wdathing/coco3-case-project/stl/main_top_right.stl

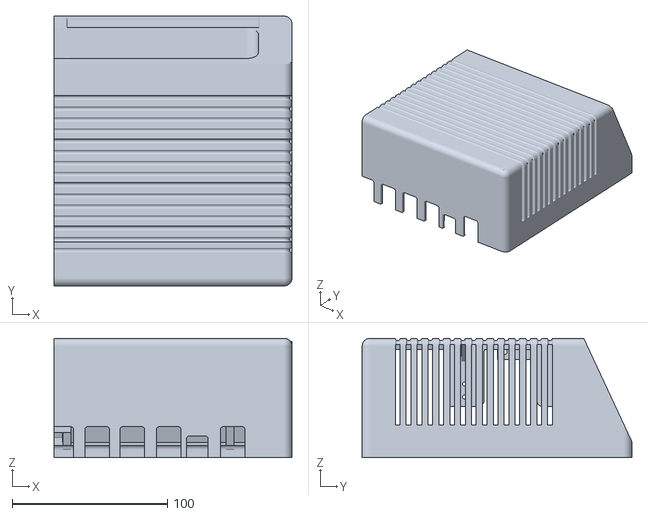
[picture p21: CAD file, 2026-10-01]
stl/main_top_right.stl
153.2 x 173.6 x 76.8
