wdathing/coco3-case-project/stl/bezel_artemis_whole.stl

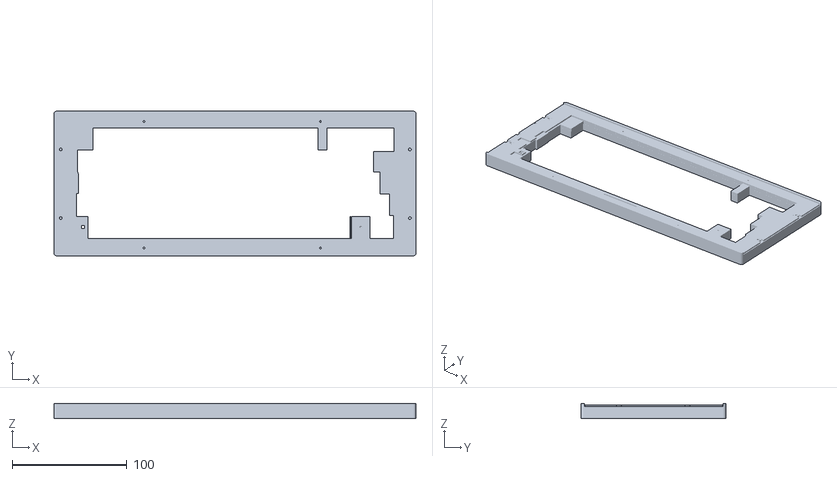
[picture p22: CAD file, 2026-09-28]
stl/bezel_artemis_whole.stl
316.0 x 126.2 x 13.3
