wdathing/coco3-case-project/stl/bezel_oem_whole.stl

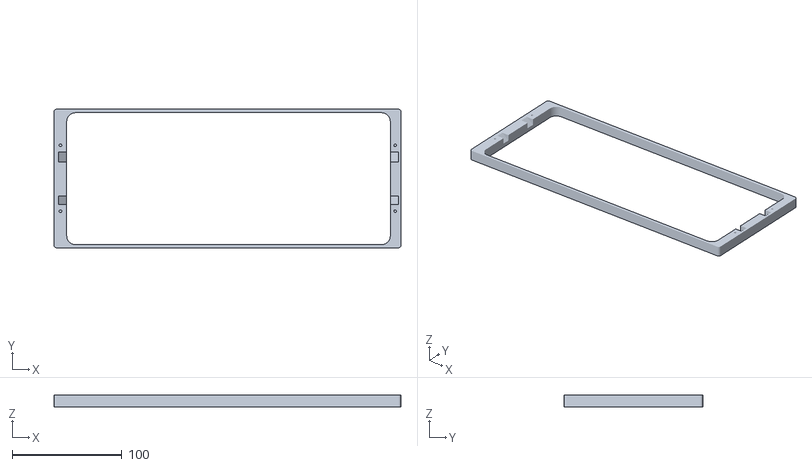
[picture p23: CAD file, 2026-09-28]
stl/bezel_oem_whole.stl
316.0 x 126.2 x 10.6
