wdathing/coco3-case-project/stl/keyboard_main_keys.stl

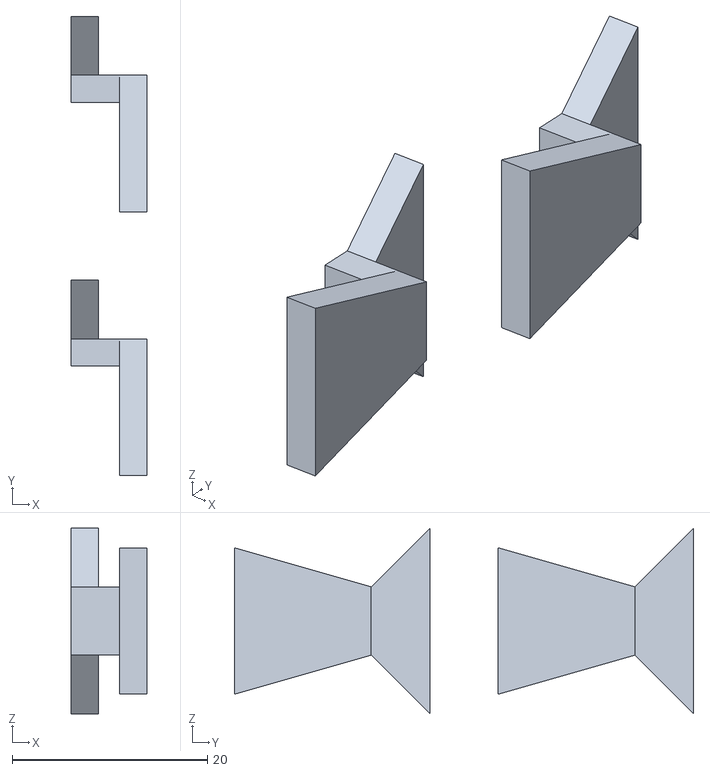
[picture p24: CAD file, 2026-09-28]
stl/keyboard_main_keys.stl
7.80 x 47.0 x 19.0
