wdathing/coco3-case-project/stl/main_faceplate.stl

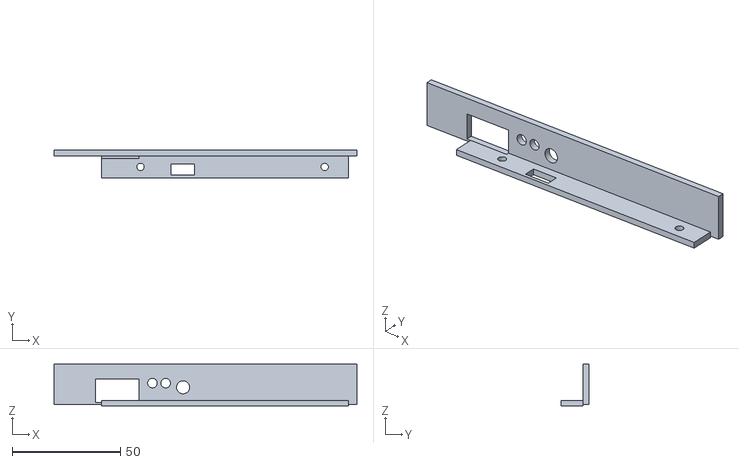
[picture p25: CAD file, 2026-09-28]
stl/main_faceplate.stl
139.8 x 12.7 x 19.4
