wdathing/coco3-case-project/stl/main_bottom_right.stl

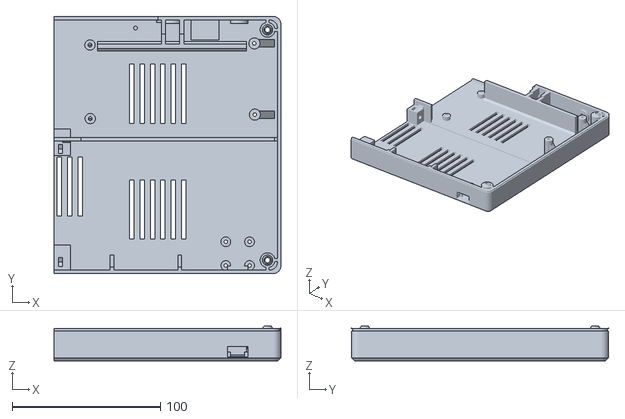
[picture p26: CAD file, 2026-09-28]
stl/main_bottom_right.stl
153.2 x 173.6 x 23.4
