wdathing/coco3-case-project/CoCo-FujiNet-Rev000.stl

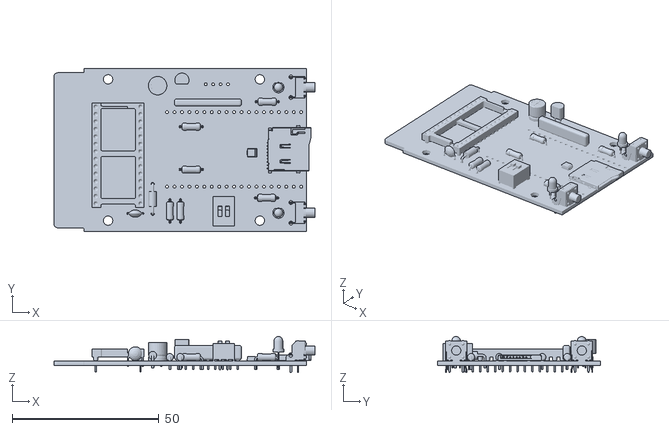
[picture p27: CAD file, 2026-09-30]
CoCo-FujiNet-Rev000.stl
88.9 x 55.4 x 12.3
