wdathing/coco3-case-project/stl/keyboard_bottom_left.stl

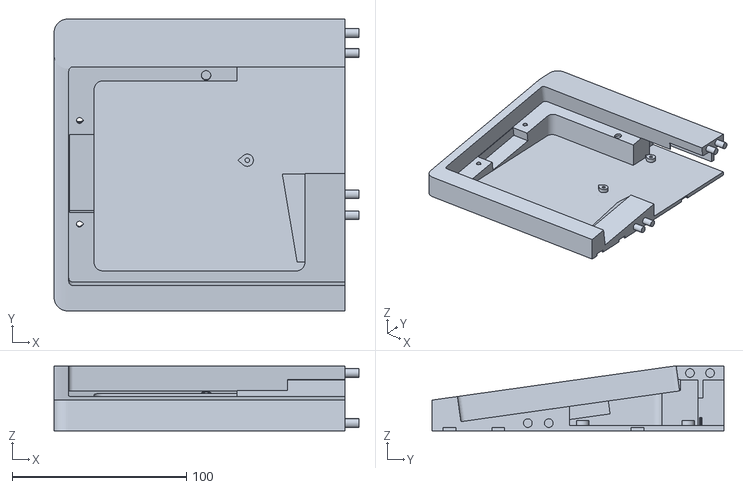
[picture p28: CAD file, 2026-10-02]
stl/keyboard_bottom_left.stl
175.0 x 167.5 x 37.2
