wdathing/coco3-case-project/split key frame.stl

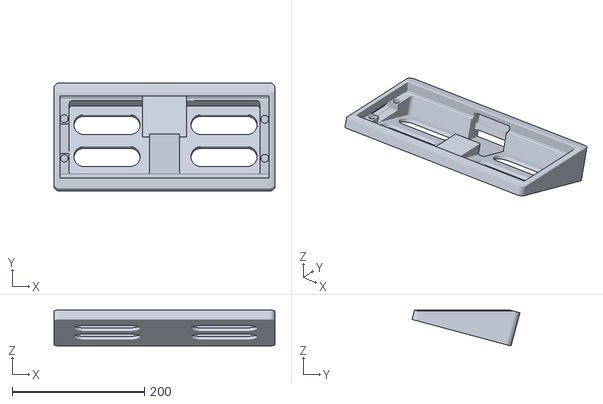
[picture p29: CAD file, 2026-09-28]
split key frame.stl
334.0 x 163.1 x 54.3
