wdathing/coco3-case-project/Coco_pico_keyb.step

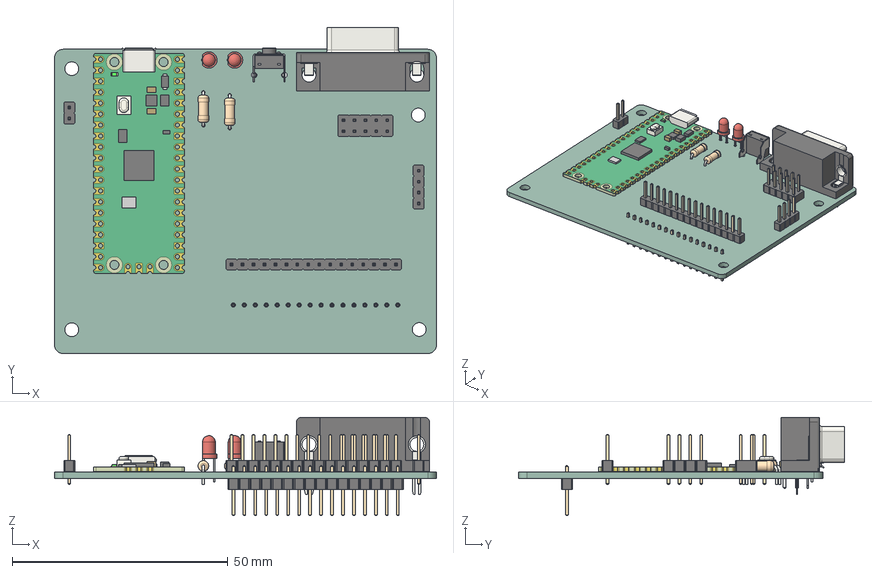
[picture p30: CAD file, 2026-09-28]
Coco_pico_keyb.step
88.5 x 75.5 x 22.7 mm
PinHeader_1x04_P254mm_Vertical
LED_D3.0mm x 2
DSUB-9_Pins_Horizontal_P2.77x2.84mm_EdgePinOffset4.94mm_Housed_ MountingHolesOffset4.94mm
PinHeader_1x02_P254mm_Vertical
PinHeader_2x05_P254mm_Vertical
RaspberryPi_Pico_Module_KiCad
R_Axial_DIN0207_L63mm_D25mm_P762mm_Horizontal x 2
SW_Tactile_SPST_Angled_PTS645Vx39-2LFS
PinHeader_1x16_P254mm_Vertical x 2
Coco_pico_keyb_PCB
