wdathing/coco3-case-project/Artemis v3 bezel.stl

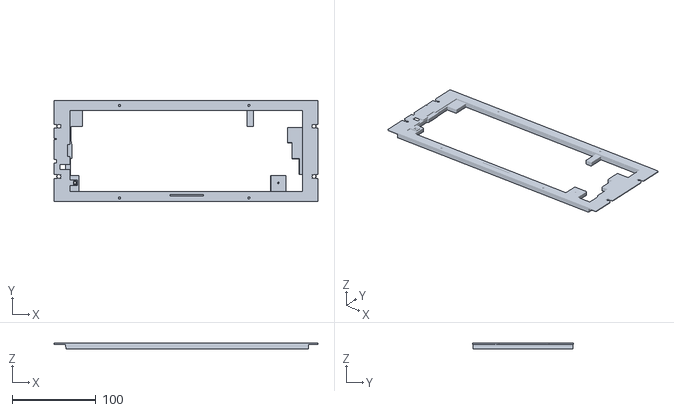
[picture p31: CAD file, 2026-09-28]
Artemis v3 bezel.stl
315.2 x 120.3 x 6.60
