wdathing/coco3-case-project/stl/floppy_filler_plate.3mf

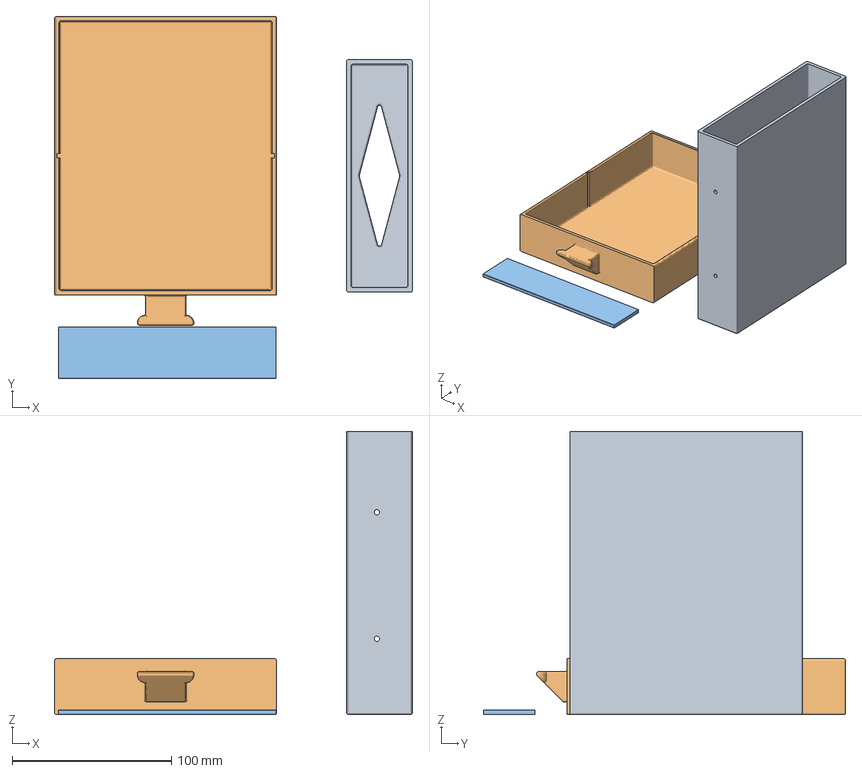
[picture p32: CAD file, 2026-10-02]
stl/floppy_filler_plate.3mf
224.7 x 227.3 x 177.8 mm
Bay.stl
Drawer.stl
Drawer_Divider.stl
