wdathing/coco3-case-project/stl/bottom_one_piece.3mf

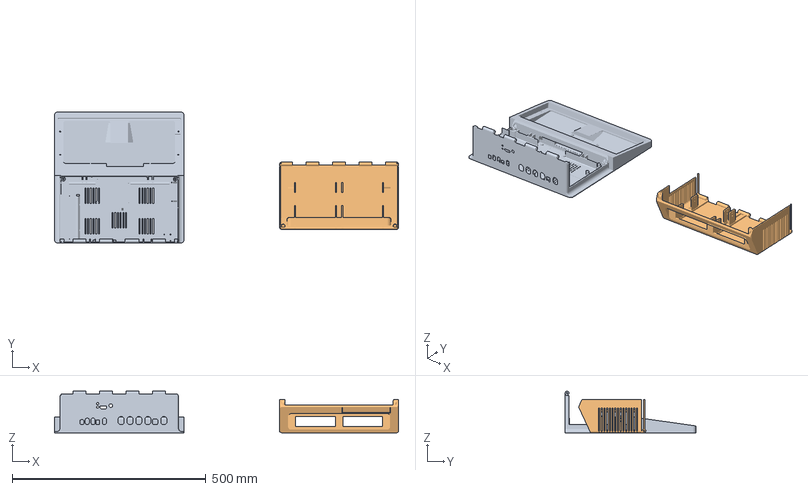
[picture p33: CAD file, 2026-10-02]
stl/bottom_one_piece.3mf
886.9 x 337.1 x 107.1 mm
bottom_one_piece.stl
main_top_whole_1p.stl
