wdathing/coco3-case-project/hinged-stls/bottom_one_piece.stl

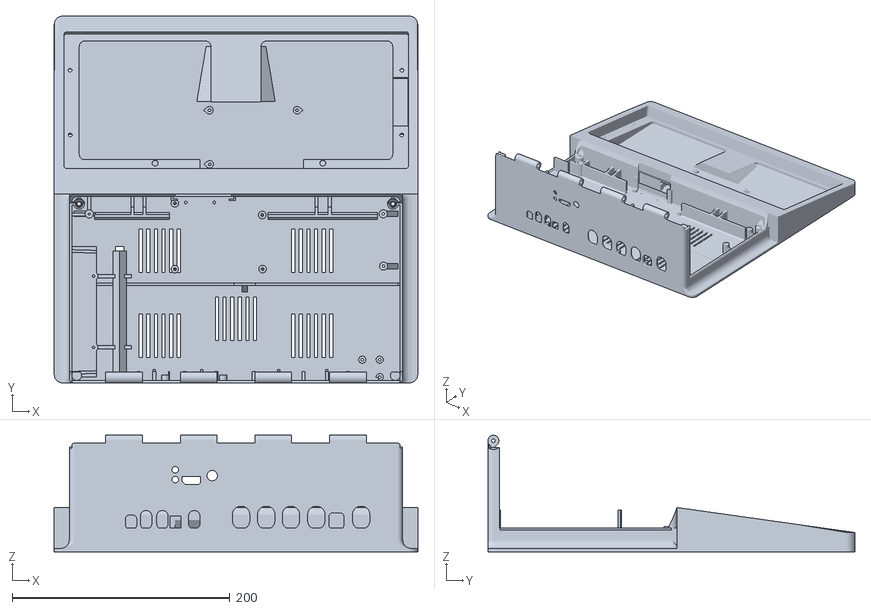
[picture p34: CAD file, 2026-10-01]
hinged-stls/bottom_one_piece.stl
334.0 x 337.1 x 107.1
