wdathing/coco3-case-project/stl/floppy_filler_clip.stl

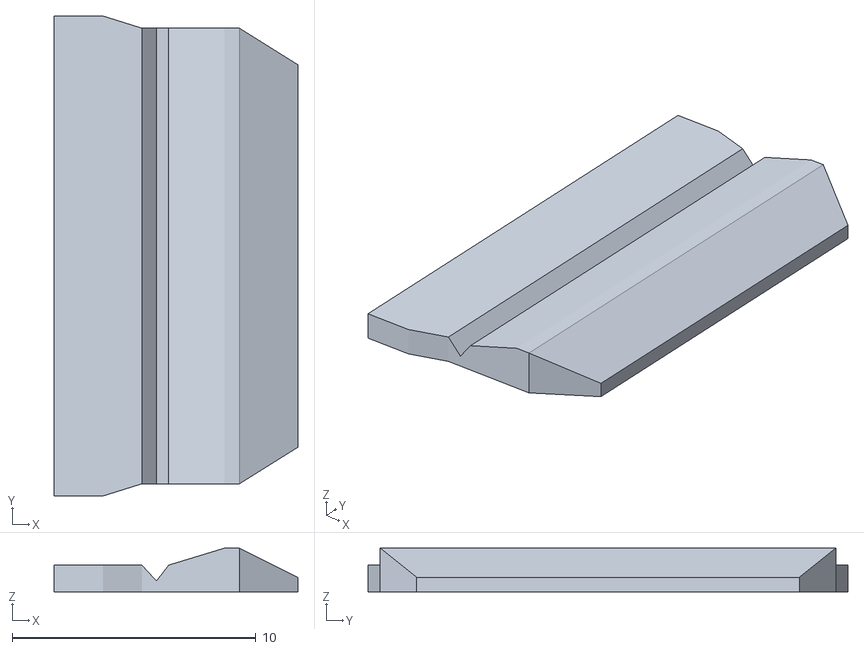
[picture p35: CAD file, 2026-09-30]
stl/floppy_filler_clip.stl
10.0 x 19.7 x 1.80
