wdathing/coco3-case-project/stl/usbc_clip.stl

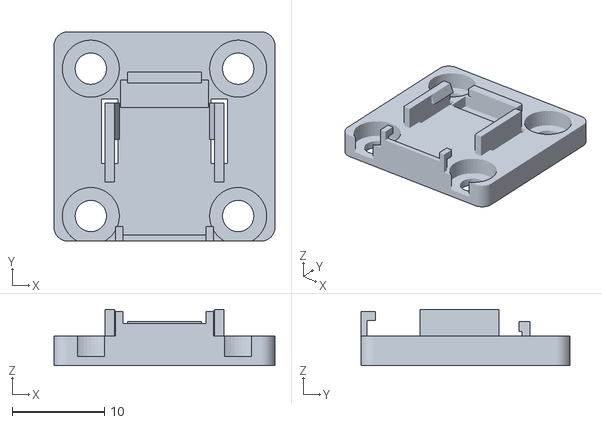
[picture p36: CAD file, 2026-09-30]
stl/usbc_clip.stl
24.0 x 22.7 x 6.10
