wdathing/coco3-case-project/stl/fujinet_tray.stl

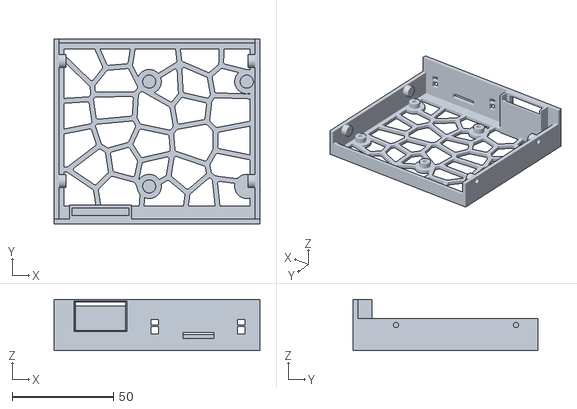
[picture p37: CAD file, 2026-09-30]
stl/fujinet_tray.stl
101.6 x 91.5 x 25.4
