wdathing/coco3-case-project/stl/keyboard_bridge_plate.stl

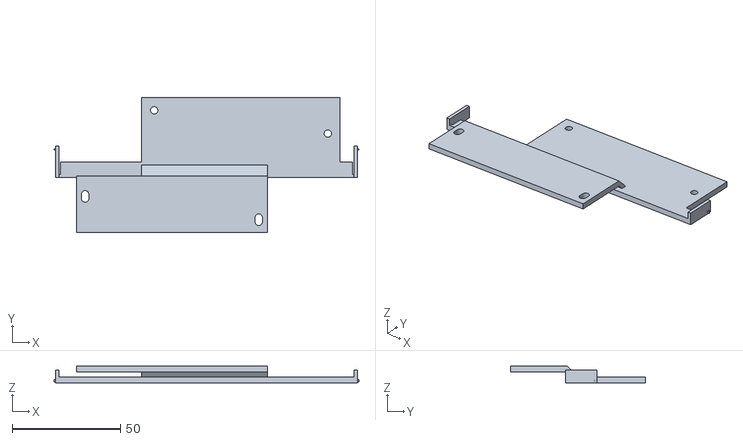
[picture p38: CAD file, 2026-09-28]
stl/keyboard_bridge_plate.stl
141.0 x 62.6 x 7.70
