wdathing/coco3-case-project/stl/bezel_oem_left.stl

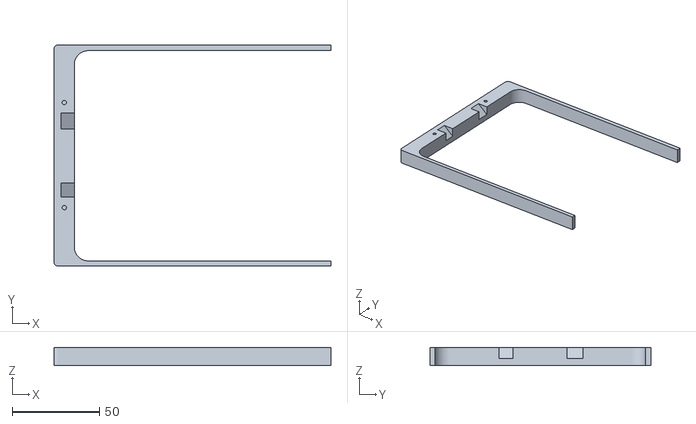
[picture p39: CAD file, 2026-09-28]
stl/bezel_oem_left.stl
158.3 x 126.2 x 10.6
