wdathing/coco3-case-project/stl/keyboard_magnet_plugs.stl

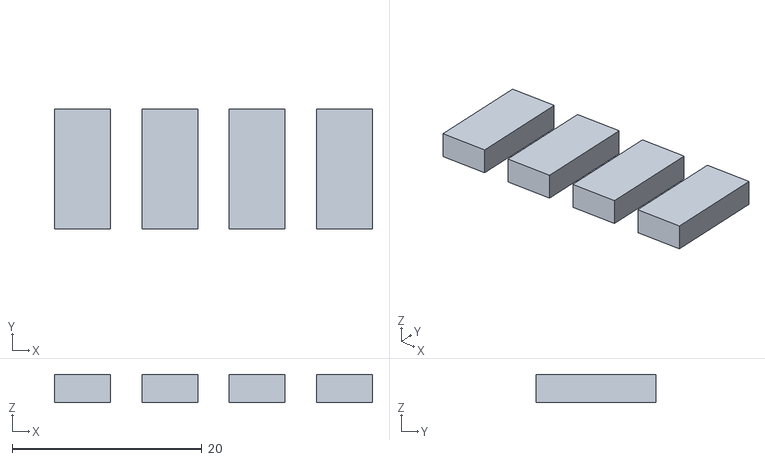
[picture p40: CAD file, 2026-09-28]
stl/keyboard_magnet_plugs.stl
33.5 x 12.6 x 2.95
