wdathing/coco3-case-project/stl/keyboard_joiner_keys.stl

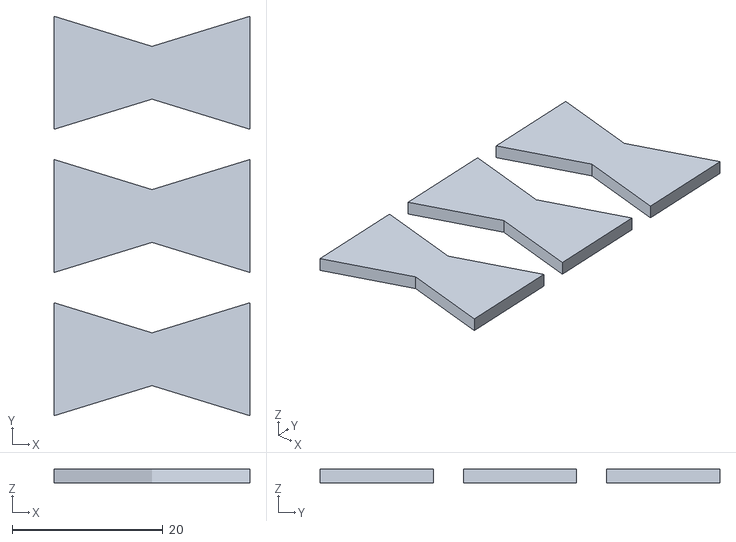
[picture p41: CAD file, 2026-09-28]
stl/keyboard_joiner_keys.stl
26.0 x 53.0 x 1.80
