wdathing/coco3-case-project/stl/keyboard_bottom_right.stl

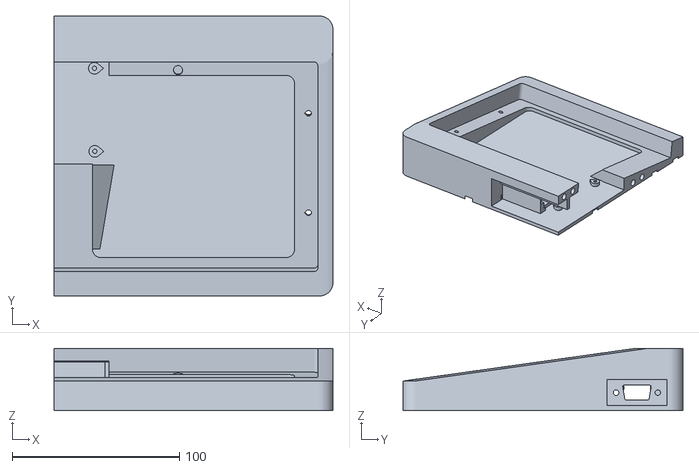
[picture p42: CAD file, 2026-09-28]
stl/keyboard_bottom_right.stl
167.0 x 167.5 x 37.2
