wdathing/coco3-case-project/stl/bezel_artemis_left.stl

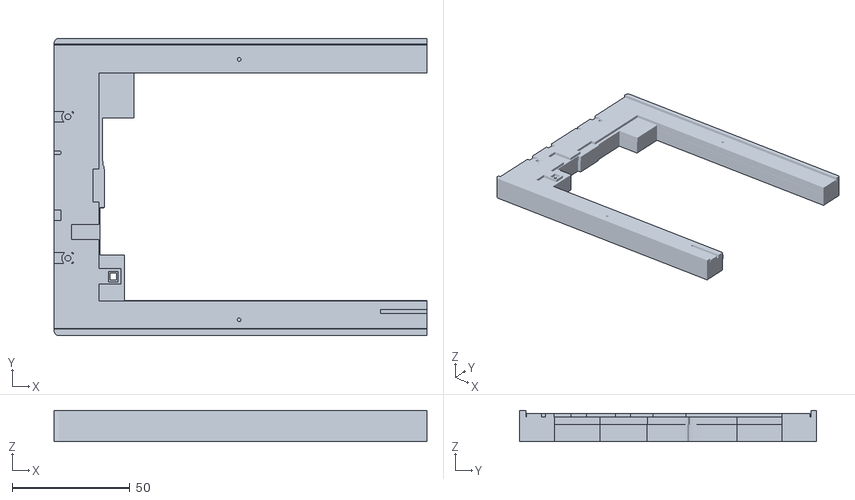
[picture p43: CAD file, 2026-09-28]
stl/bezel_artemis_left.stl
158.3 x 126.2 x 13.3
