wdathing/coco3-case-project/stl/keyboard_faceplate.stl

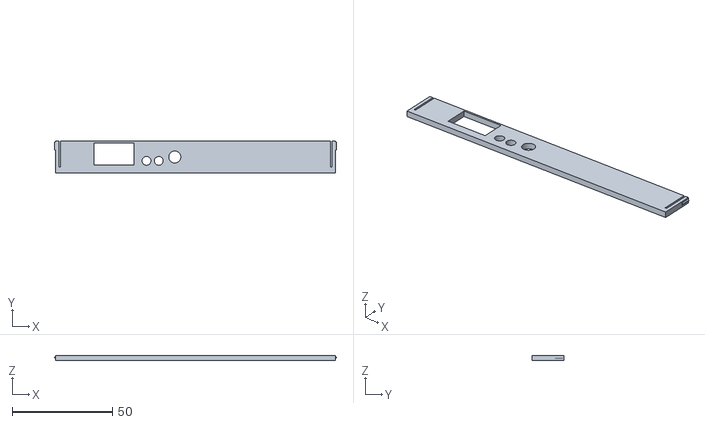
[picture p44: CAD file, 2026-09-28]
stl/keyboard_faceplate.stl
141.0 x 15.8 x 2.70
