wdathing/coco3-case-project/stl/bezel_artemis_right.stl

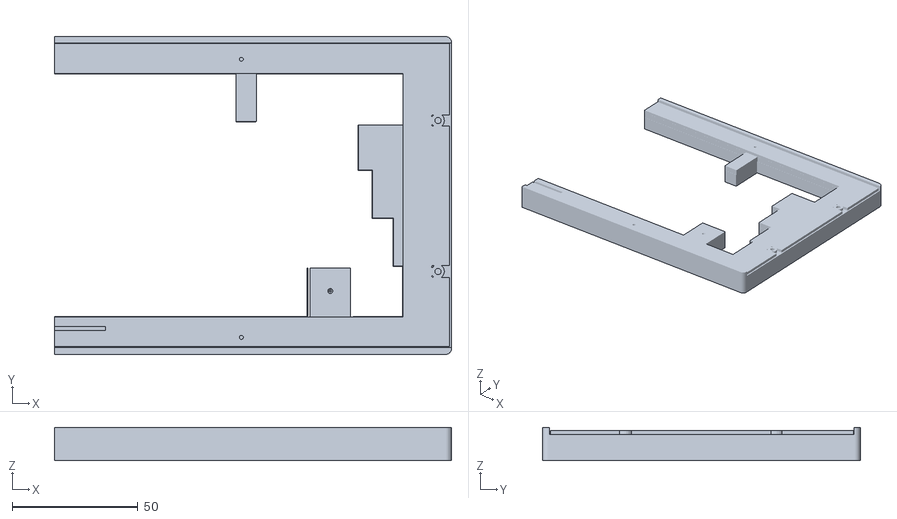
[picture p45: CAD file, 2026-09-28]
stl/bezel_artemis_right.stl
157.8 x 126.2 x 13.3
