wdathing/coco3-case-project/coco3_case.scad

// SPDX-License-Identifier: CC-BY-4.0
// Copyright (c) 2026 Bill Athing -- https://github.com/wdathing/coco3-case-project
// ============================================================================
// CoCo3 (26-3334) "CoCo4-style" 3D Printable Case  —  Parametric OpenSCAD
// ============================================================================
// DATA PROVENANCE — read this before changing numbers:
//
//   REAL / MEASURED data (do not guess-adjust without re-checking source):
//     - Motherboard outline, 3 standoff-hole positions+diameters, 12 named
//       connector positions/rotations  -> parsed directly from coco3.step
//       (KiCad STEP export of the qbancoffee/coco_motherboards 26-3334 board).
//     - Keyboard-controller PCB outline, 5 standoff holes, connector
//       positions -> parsed directly from Coco_pico_keyb.step (Pico-based
//       keyboard interface board).
//     - Boss height (22.25mm) and case wall thickness (2.4mm ABS) -> given
//       by user, measured from a stock case.
//     - Port identities (JK1/JK2 joystick, JK3 serial, JK4 cassette, J5A/J5B
//       composite video/audio, SW1 power, SW3 ch3/4, SW2 reset, CN1
//       cartridge -- confirmed RIGHT SIDE panel not rear, CN3 RGB
//       bottom-mounted) -> confirmed by user + Tandy service manual text.
//
//   PLACEHOLDER data (flagged TODO below, safe defaults, MUST verify before
//   printing final parts):
//     - oem_foot_height: stock rubber foot height was never measured/found;
//       Multipak card-edge slots have several mm of vertical play so this is
//       low-risk, but true it up if you can measure a stock foot.
//     - keyboard_unit_* : real CoCo keyboard mechanical envelope is NOT YET
//       measured (user is getting real numbers). Everything about the
//       keyboard tray floor/window is parametric off these 4 numbers, so
//       updating them re-shapes the whole keyboard tray automatically.
//     - Panel cutout SIZES for DIN4/5/6, RCA, cartridge slot, power switch,
//       reset button, slide switch: real bounding boxes only resolved
//       cleanly for JK3 (serial) and the two power jacks; everything else
//       uses standard commodity connector dimensions (DIN shells are
//       standardized regardless of pin count; RCA jacks are standardized;
//       card-edge slot width is derived from standard .1" 40-pos edge-card
//       spec). Adjust per-connector if your actual parts differ.
//     - Pico USB-port edge/orientation on the keyboard PCB (for the rear
//       keyboard-case cutout) and J6 DE-9 breakout orientation: positions
//       are real, but which edge the connector body actually exits from
//       wasn't resolved from the STEP nesting. Verify against the physical
//       board before printing the keyboard rear panel.
//
// UNITS: millimeters throughout. Y=0 is the REAR-panel edge of the board;
//        Y+ increases toward the FRONT (keyboard side). X+ = rightward as
//        viewed from the front (matches the real CN1 cartridge-slot side).
//        Z+ = up.
// ============================================================================

/* [Printer / Global] */
bed_x = 250;              // printer bed X (mm)   
bed_y = 250;              // printer bed Y (mm)
bed_z = 250;              // printer bed Z (mm) - not used for splitting yet (parts are short)
split_margin = 6;         // extra clearance subtracted from bed size before deciding to split
wall            = 2.4;    // shell wall thickness (matches OEM spirit)
tol             = 0.25;   // general fit clearance
// Fastening method for every M3 screw post/boss THAT THREADS DIRECTLY INTO
// PRINTED PLASTIC throughout the project (board standoffs' own real
// mounting-hole DIAMETERS on the PCB itself -- e.g. the 3.2mm clearance
// holes on the kbpcb board -- are fixed by the physical boards and
// unaffected by this; this only sets the PILOT hole printed into each
// post/boss). Per direction: reintroduced as a build-time choice (was
// self-tap-only for a while) -- "self_tap": screw threads directly into
// the plastic, pilot sized for good bite (2.6mm, per direction, up from
// the earlier 2.5mm placeholder -- "too big" reported at 2.5, i.e. that
// was already undersized/binding, not oversized -- true up further
// against the specific screws you actually use). "heat_set": a threaded
// brass insert gets pressed/heat-staked into the pilot first, then a
// machine screw threads into THAT -- pilot sized to the insert's own OD
// (4.0mm, per direction), not the screw.
screw_mount_type = "self_tap"; // "self_tap" or "heat_set"
m3_pilot_d = (screw_mount_type == "heat_set") ? 4.0 : 2.6;
$fn             = 48;     // circle resolution (raise for final render, lower for fast preview)

/* [Keyboard attachment mode] */
// true  = keyboard shell is structurally merged with the main shell (one
//         continuous printed seam, reinforced rib, NOT separable)
// false = keyboard shell is a separate, detachable part: lip-and-socket +
//         magnets join it to the main shell
keyboard_attached = false;
// (keyboard_attached=true = the BOLTED variant: no magnets; 3 M3 screws
//  from inside the main case clamp the keyboard shell on -- see
//  main_kb_bolt_holes() / kb_bolt_pilots(). false = detachable, magnets.)
// Rectangular lip/socket lugs (main_lip_socket / kb_socket_pockets) --
// separate from the magnet pockets, which stay on either way. Per
// direction, turned off for now (magnets alone are enough of an
// interlock to test with); flip back to true to bring the tabs back.
lip_socket_tabs_enabled = false;
// ONE-PIECE BOTTOM (big printers, e.g. the Sovol SV08 Max): the main bottom and the keyboard shell print as a single
// part ("bottom_one_piece"). The keyboard goes on the same 5mm stick-on feet as the main case (kb_feet), so the two
// undersides are one flat plane -- no supports. That lifts the keyboard 5mm, and the main top's front skirt (which is
// derived from the keyboard's shelf height) grows 5mm with it: print the main top from THIS setting too
// (stl/main_top_whole_1p.stl). No magnets, bolts or joiner keys -- keyboard_attached is ignored.
one_piece_bottom = false;
// HINGED LID: the back plate (rear wall, with all its connector cutouts and the DV I/O panel) becomes part of the
// bottom, and the rest of the top is a lid that swings up on a hinge along the rear top edge -- the drives ride up
// with it -- for access to the drive bays and the motherboard. See HINGED LID near the seam lugs. Parts keep their
// usual names (main_top_* = the lid, main_bottom_* / bottom_one_piece include the plate); export them to hinged-stls/.
main_hinged = false;
// The one-piece base WITH the hinged lid gets extra strength work (all gated on this, so no other build changes):
// solid posts up the two back corners, the decorative groove round the base's top edge filled across the back (it sat
// under the back plate as a support-hungry notch; kept along the sides), the rear PCB ribs' wall step carried up the
// plate as fins (the leftmost rib moved to sit centred between its two ports), and much rounder rear port openings.
onepiece_hinged = one_piece_bottom && main_hinged;
kb_join_magnets = !one_piece_bottom && !keyboard_attached;
kb_join_bolts   = !one_piece_bottom && keyboard_attached;
kb_join_keys    = !one_piece_bottom;   // the stepped bow-tie keys across the keyboard/main seam

/* [Height stack — Multipak compatibility] */
oem_boss_height   = 22.25;  // REAL (measured by user)
oem_floor_t       = 2.4;    // REAL (measured/estimated by user)
oem_foot_height   = 3.0;    // TODO PLACEHOLDER — verify against a stock unit if possible
target_pcb_top_above_desk = oem_foot_height + oem_floor_t + oem_boss_height;

new_foot_height   = 5.0;    // this design's own foot height (can differ from OEM) --
                             // 5mm adhesive rubber stick-on feet. standoff_height
                             // below solves to compensate automatically so the
                             // PCB (and cart slot) height above the desk stays
                             // fixed at target_pcb_top_above_desk regardless of
                             // this value -- that's the whole point of this
                             // formula, so just changing this one number is the
                             // correct/complete fix, no other height edits needed.
new_floor_t       = wall;   // this design's own floor thickness
standoff_height   = target_pcb_top_above_desk - new_foot_height - new_floor_t;
echo(str("Computed standoff height above case floor: ", standoff_height, " mm"));
echo(str("Target PCB-top height above desk (must match OEM for Multipak fit): ", target_pcb_top_above_desk, " mm"));

/* [Case shape / aesthetic — CoCo4-prototype-inspired wedge] */
case_margin        = 13.17; // clearance from board edge to inner wall
                            // Sized for the cart-slot side: CN1 is confirmed
                            // 40mm from the case wall on a real CoCo3;
                            // proposed 25mm here (tighter, still comfortable
                            // for the cantilevered cartridge). CN1 sits
                            // 11.83mm in from the board edge, so the wall
                            // needs to be 25 - 11.83 = 13.17mm out from the
                            // board edge to hit that. Applied uniformly (all
                            // 4 sides use the same margin) rather than only
                            // on the cart side, for simplicity -- total
                            // width becomes 280 + 2*13.17 = 306.3mm, still
                            // under 320mm. This also comfortably supersedes
                            // the earlier 6->9 bump that was only sized for
                            // the CN3 collar's own clearance need.
rear_margin         = case_margin - 9; // ~4.17mm -- per direction, after a
                            // real dry-fit of the physical motherboard into
                            // a partial print: the board's rear edge fell
                            // about 9mm short of reaching the rear wall.
                            // case_margin (13.17mm) was sized for the CN1
                            // cart-slot clearance need on the SIDE wall and
                            // just applied uniformly everywhere for
                            // simplicity -- it was never validated against
                            // the rear panel specifically, where the real
                            // connectors (DIN jacks etc.) mount close to the
                            // board edge and need the wall close behind
                            // them, not 13mm of open air. Used ONLY for the
                            // -Y (rear) side of the footprint everywhere
                            // that matters (outer shell, inner cavity, rear
                            // support ribs, raceway, rear panel notches) --
                            // front/left/right keep the original case_margin.
// front_deck_h / rear_tower_h are computed further down (see "TOP SHELL
// STYLING" below main_depth) -- they depend on parting_h and the floppy bay
// stack, neither of which exist yet at this point in the file.
corner_r           = 5;    // outer corner rounding radius -- matches the
                            // explicit 5mm 3D edge fillet request (see
                            // edge_fillet_r / rounded_footprint_solid
                            // below), used consistently for both. Applies
                            // directly to the BOTTOM shell and the TOP
                            // shell's vertical corners; the top shell's own
                            // rounded-top-rim treatment is not implemented
                            // yet (it's a wedge, not a plain box, so the
                            // hull()-cap technique used for the bottom
                            // shell doesn't directly apply) -- flag if you
                            // want that pursued too.

// Top/bottom clamshell split, flat across the whole footprint (simplest to
// print and assemble). Per a photo of a real stock case bottom: the OEM
// bottom shell is just a shallow tray (floor, standoffs, no connector
// cutouts) and the TALL top shell carries all the connector panel cutouts
// and louvers.
//
// parting_h = standoff_height + pcb_edge_lip_height: the bottom tray's
// wall stops right at the top of the PCB-edge lip (see main_pcb_edge_lip_
// relief further down) -- NOT higher, with extra headroom, as an earlier
// version of this file had it (parting_h = 34, ~10mm above the lip). That
// extra height was a real bug, not just cosmetic: a cartridge slides in
// at roughly PCB height, but the cart-slot notch is cut into the TOP
// shell starting at parting_h -- if the bottom tray's wall is still solid
// well above PCB height, it physically blocks the cartridge from ever
// reaching that notch. The cart guide walls are the one deliberate
// exception: they rise well above parting_h into the top shell's (hollow)
// interior, to guide the cartridge continuously from PCB height up to the
// slot opening.
pcb_edge_lip_height = 1.6; // matches PCB thickness -- see main_pcb_edge_lip_relief()
parting_h = standoff_height + pcb_edge_lip_height;

louver_count       = 11;
louver_w           = 3.0;
louver_gap         = 4.0;
louver_depth       = wall + 1.0; // cut all the way through the wall + a hair

/* [Keyboard mechanical envelope — TODO: replace with real measurements] */
keyboard_unit_w   = 330;  // PLACEHOLDER, proportioned from OEM 375mm cabinet width
keyboard_unit_d   = 130;  // PLACEHOLDER
keyboard_unit_h   = 20;   // PLACEHOLDER (keyswitch travel + plate)
keyboard_deck_margin = 10; // bezel width around the keyboard window

// ============================================================================
// MOTHERBOARD GEOMETRY (real, from coco3.step)
// ============================================================================
// board_pt() re-bases KiCad's native board coordinates (origin at a board
// corner, rear-panel connectors clustered near Y=0, board extends to
// Y=-156.26) into a first-quadrant, rear-positive-Y frame used everywhere
// else in this file.
BOARD_X_OFF = 31.48;
// board_pt is mirrored in X (248.52 - x, not x + BOARD_X_OFF) relative to
// the original transform. The original mapping put CN1 (cart slot) at
// high X and labeled that "right as viewed from the front" -- but the
// rigorous camera math for a viewer standing in front of the machine
// facing the rear (facing -Y) gives screen-right = -X, not +X (verify with
// a compass: face north, right hand points east; face south instead, right
// hand points west). So high-X was actually the viewer's LEFT. Confirmed
// against a real photo of the motherboard (coco2.jpg): viewed from near
// the keyboard looking toward the rear, the real card-edge connector is on
// the photographer's right -- which requires it to sit at LOW X once Y=0
// is correctly fixed as the rear (there's no ambiguity left on that point:
// every rear-panel connector clusters there). 248.52 = board_w -
// BOARD_X_OFF, chosen so the mirrored outline still spans exactly [0, 280].
function board_pt(x,y) = [248.52 - x, -y];

board_outline_raw = [
 [217.390,-1.000],[216.390,-0.000],[1.000,0.000],[0.000,-1.000],
 [-0.000,-16.320],[1.000,-17.320],[10.200,-17.320],[10.200,-87.400],
 [-30.480,-87.410],[-31.480,-88.410],[-31.480,-92.100],[-30.480,-93.100],
 [-28.400,-93.100],[-28.400,-95.920],[-30.480,-95.920],[-31.480,-96.920],
 [-31.480,-110.310],[-30.480,-111.310],[-28.240,-111.310],[-28.240,-113.980],
 [-30.480,-113.980],[-31.480,-114.980],[-31.480,-155.260],[-30.480,-156.260],
 [247.520,-156.260],[248.520,-155.260],[248.520,-122.070],[247.520,-121.070],
 [233.370,-121.070],[233.370,-97.970],[247.520,-97.970],[248.520,-96.970],
 [248.520,-24.760],[247.520,-23.760],[233.530,-23.760],[233.530,-12.670],
 [232.530,-11.670],[217.390,-11.670]
];
board_outline = [ for (p = board_outline_raw) board_pt(p[0], p[1]) ];
board_w = 280;     // bounding-box width  (X), real
board_d = 156.26;  // bounding-box depth  (Y), real
board_thickness = 1.55; // real

// standoff holes: [x, y, hole_diameter] -- real. First 3 were already known;
// the last 2 were found by re-parsing coco3.step directly (isolating the
// PCB's own solid body, extracting every CIRCLE entity, filtering to the
// 2.5-4.5mm mounting-screw diameter range, and checking for isolated
// corner placement vs. dense component-grid clustering). Those two are
// actually SLOTTED/oblong holes in the real board (a pair of 3.5mm circles
// ~2mm apart on X, not a single round hole -- likely intentional to
// absorb tolerance/thermal slop); modeled here as a plain round 3.5mm hole
// at the slot's midpoint, a reasonable simplification but not a literal
// match if you want the oblong shape reproduced exactly.
board_standoffs = [
  for (h = [ [239.389,-93.963,4.0], [239.389,-28.558,4.0], [-27.050,-103.160,3.5],
             [-26.760,-151.260,3.5], [243.360,-151.260,3.5] ])
    [ board_pt(h[0],h[1])[0], board_pt(h[0],h[1])[1], h[2] ]
];

// named connectors: [refdes, x, y, z_above_board, rot_deg, kind]
// z_above_board is the component's local Z origin from the STEP file; not
// used for cutout height directly (panel cutouts are sized generously) but
// kept for reference / future refinement.
board_connectors = [
  ["SW1", board_pt(16.30,  -9.27)[0], board_pt(16.30,  -9.27)[1],  7.31, -180, "power_switch"],
  ["JK1", board_pt(34.74, -12.29)[0], board_pt(34.74, -12.29)[1],  1.60,  180, "din6"],
  ["JK2", board_pt(58.08, -12.29)[0], board_pt(58.08, -12.29)[1],  1.60,  180, "din6"],
  ["JK3", board_pt(80.74,  -1.24)[0], board_pt(80.74,  -1.24)[1],  1.60,  180, "din4"],
  ["JK4", board_pt(103.79, -1.49)[0], board_pt(103.79, -1.49)[1], 11.76,  180, "din5"],
  ["J5A", board_pt(176.10, -1.74)[0], board_pt(176.10, -1.74)[1],  2.87,  180, "rca"],
  ["J5B", board_pt(191.10, -1.74)[0], board_pt(191.10, -1.74)[1],  2.87,  180, "rca"],
  ["SW3", board_pt(161.09, -3.55)[0], board_pt(161.09, -3.55)[1],  3.50,   90, "slide_switch"],
  ["SW2", board_pt(204.87, -3.91)[0], board_pt(204.87, -3.91)[1],  1.60,  180, "reset_button"],
  ["CN1", board_pt(236.69,-61.13)[0], board_pt(236.69,-61.13)[1],  6.60,  -90, "cart_slot"],   // RIGHT-SIDE panel!
  ["CN3", board_pt(230.31,-140.51)[0],board_pt(230.31,-140.51)[1], -0.09,  90, "rgb_din8"],
];

// ============================================================================
// KEYBOARD-CONTROLLER PCB GEOMETRY (real, from Coco_pico_keyb.step) --
// UPDATED per a revised board (smaller/simpler outline, "easier to work
// with and cheaper"; re-extracted via a proper STEP entity-graph parse
// this time, not hand-tracing, then cross-checked against the mounting
// holes' own real KiCad coordinates -- all 4 matched exactly). J2, a real
// DSUB-9 (DE-9) connector footprint now on the board, is deliberately NOT
// wired into the case yet -- per direction, "that will be implemented in
// a different deployment scenario."
//
// kbpcb_pt FIXED per direction ("upside down... rotate 180 degrees... align
// to the front edge"): the old formula [x-79.5, -y-28] flipped only the raw
// STEP Y axis (determinant -1 -- a MIRROR of the real board, not a rigid
// placement) and put the panel edge (USB/LEDs/button, all clustered near
// raw Y=-27.5) at the LOW end of local Y -- i.e. toward the case's rear,
// with the J1/J3 ribbon-header edge (raw Y=-98) toward the front instead.
// Both wrong. New formula copies raw X and Y directly (no flip at all --
// determinant +1, a proper placement) and re-zeros against the real
// outline's exact min corner (79.0, -98.0) instead of the old rounded
// (79.5, 28) constants, so the panel edge now lands at local Y=kbpcb_d
// (the HIGH end) -- the edge that gets placed toward the case's front wall
// below.
// ============================================================================
function kbpcb_pt(x,y) = [x - 79.0, y + 98.0];

// Real outline is a plain rounded rect now (2mm corner radius, not
// consumed by any cut geometry below -- kbpcb_w/kbpcb_d, the bounding
// box, are what's actually used -- so the corner rounding is just kept
// here for reference, not modeled).
kbpcb_outline_raw = [
 [167.5,-27.5],[167.5,-98.0],[79.0,-98.0],[79.0,-27.5]
];
kbpcb_outline = [ for (p = kbpcb_outline_raw) kbpcb_pt(p[0], p[1]) ];
kbpcb_w = 88.5; kbpcb_d = 70.5; kbpcb_thickness = 1.51; // real, updated board

kbpcb_standoffs = [
  for (h = [ [163.275090,-42.745040,3.2],[83.000000,-32.000000,3.2],
             [83.000000,-92.500000,3.2],[163.500000,-92.433792,3.2] ])
    [ kbpcb_pt(h[0],h[1])[0], kbpcb_pt(h[0],h[1])[1], h[2] ]
];

pico_pos = kbpcb_pt(98.575, -53.97);
// The installed 1x16 ribbon header (raw x 118.8..159.4): its CENTRE, in board-local x, is what gets centred on the case (under the
// keyboard's ribbon cable / on the main case's centreline) -- NOT the Pico/USB jack, which sits 40.5mm to its left on the board and
// has no need to be centred.
kbpcb_hdr_cx = kbpcb_pt(139.1, 0)[0];   // = 60.1

// New on the updated board: 2 LEDs (D1/D2, 3mm round) and a tactile
// button (SW1) needing case access -- per direction. R1/R2 are just their
// current-limit resistors, no case feature needed.
// REAL component data, measured off Coco_pico_keyb.stl (the stuffed board; same KiCad frame as the
// STEP, Z=0 at the PCB bottom). LED/button X are the BODY centres, not the pad positions the earlier
// numbers used (113.5 / 119.46 / 126.5) -- those were 1.1 / 1.3 / 2.3 mm off the real parts.
kbpcb_led1_pos = kbpcb_pt(114.60, -30.0);  // D1  (body x 113.27..115.93)
kbpcb_led2_pos = kbpcb_pt(120.73, -30.0);  // D2  (body x 119.23..122.24)
kbpcb_button_pos = kbpcb_pt(128.75, -31.0); // SW1 (cap x 125.05..132.45, 7.4 wide, 6.9 tall)
kbpcb_led_z = 5.43;       // LED lens centre above the PCB top
kbpcb_btn_z = 3.49;       // button cap centre above the PCB top
kbpcb_usb_x = 98.33;      // USB jack centre X (jack is 11.9 wide, 3.7 tall)
kbpcb_usb_z = 1.93;       // USB jack centre above the PCB top
kbpcb_comp_above = 8.62;  // TALLEST part above the PCB top (the 2.54mm headers)
kbpcb_pin_below  = 2.4;   // pin tails below the PCB bottom
kbpcb_edge_poke  = 0.33;  // the USB jack pokes this far past the board's USB edge

// ---- SHARED FACEPLATE WINDOW ---------------------------------------------------------------------------------------
// The keyboard's back-of-board wall and the main case's front wall carry the SAME window, closed by the SAME printed plate
// (keyboard_faceplate): USB / LED / button openings for a controller board, sitting 1.2mm from the plate exactly as the
// board sits in the keyboard. Both boards are positioned by their ribbon header (on the case centreline), so a plate centred
// on that line lines up with either board. Nothing is screwed on: the plate SNAPS in from the outside. Each end of the plate has
// a flexible finger (a slot cut beside the end, in the plate's own plane so it flexes along the layers) with a barb on its tip
// that clicks into a groove in the window's end wall. The plate seats against solid on its inner side (the keyboard's tunnel
// ends, the main case's stop blocks). To release, push it out from the inside, or pry the ends. With the plates out, the two
// windows line up into one tunnel through the seam (main X 70..210 = keyboard kx 97..237) for the keyboard ribbon, and the
// bridge plate crosses it.
fp_len = 140;        // window length (X), centred on the header line
fp_z0 = 3;           // window bottom (both frames: the keyboard's floor top; main: just above its 2.4 floor)
fp_z1 = 19;          // KEYBOARD window top only, now: the board's tallest part at the edge tops out ~z 16, and above this the keyboard's own
                      // tunnel roof continues (see kb_plate_slot()). The main bottom uses main_fp_z1 below instead -- its front wall is only
                      // parting_h (21.85) tall, and fp_z1=19 left just a ~2.85mm sliver of wall above the window there, too thin to survive
                      // printing/handling. main_fp_z1 runs the window and plate all the way up to the parting line instead, removing that
                      // sliver entirely (the TOP shell's own front wall picks up right where the plate leaves off).
main_fp_z1 = parting_h;   // flush with the parting line -- no clearance gap left above it (0.3mm still showed as a visible sliver in F6)
fp_t = 2.7;          // plate thickness
fp_clr = 0.1;        // press-fit clearance per side -- tune on a test fit (FDM holes run small)
fp_out_gap = 0.1;    // plate outer face sits this far inside the wall's outer face
// snap fingers
fp_finger_l = 13;    // finger length (Z), from the plate's bottom edge up to where it is joined to the plate
fp_finger_w = 1.6;   // finger width (X): 1.6 x 13 flexes ~0.6mm at ~0.7% strain
fp_slot_w   = 0.8;   // slot beside the finger (room to flex)
fp_barb_h   = 0.6;   // how far the barb sticks out of the plate's end face
fp_barb_z0  = 0.4;   // barb starts this far above the plate's bottom edge ...
fp_barb_zl  = 4;     // ... and is this long
fp_groove_clr = 0.15;
// Barb profile in (u = out of the plate's end, v = up the plate's thickness from its inner face). The plate goes in inner face
// first, so the leading flank (small v) is the gentle one (~40 deg) and the trailing flank (large v) is steeper (~50 deg):
// easy to push in, deliberate to pull out.
module fp_barb_2d(grow = 0) {
    offset(delta = grow) polygon([[-0.2, 0.6], [fp_barb_h, 1.5], [fp_barb_h, 1.7], [-0.2, 2.2]]);
}
// x0/x1: the plate's two end faces; y0: its inner face; z0: its bottom edge (any frame -- keyboard or main)
module fp_barbs(x0, x1, y0, z0) {
    translate([0, 0, z0 + fp_barb_z0]) linear_extrude(height = fp_barb_zl) {
        translate([x0, y0]) mirror([1, 0]) fp_barb_2d();
        translate([x1, y0]) fp_barb_2d();
    }
}
module fp_grooves(x0, x1, y0, z0) {      // cut into the shell's window end walls
    translate([0, 0, z0 + fp_barb_z0 - fp_groove_clr]) linear_extrude(height = fp_barb_zl + 2*fp_groove_clr) {
        translate([x0, y0]) mirror([1, 0]) fp_barb_2d(fp_groove_clr);
        translate([x1, y0]) fp_barb_2d(fp_groove_clr);
    }
}
module fp_finger_slots(x0, x1, y0, z0) {
    translate([x0 + fp_finger_w, y0 - 1, z0 - 1]) cube([fp_slot_w, fp_t + 2, fp_finger_l + 1]);
    translate([x1 - fp_finger_w - fp_slot_w, y0 - 1, z0 - 1]) cube([fp_slot_w, fp_t + 2, fp_finger_l + 1]);
}

// ============================================================================
// GENERIC HELPERS
// ============================================================================
// The case's exterior is a plain rounded rectangle sized around the board's
// bounding box -- NOT contour-hugging the PCB's own notches/tab. Confirmed
// against a photo of a real stock case bottom: the OEM enclosure is a
// simple rounded rectangle, not shaped to the board outline. (An earlier
// version of this file offset the real board_outline directly for the case
// exterior; besides not matching the reference case, offsetting outward
// past small notches/teeth in that outline self-intersects and produces
// sawtooth artifacts. The board outline itself is still used for standoff
// and connector placement -- just not for the case's own exterior shape.)
// `rear` optionally overrides the -Y (rear-wall) margin independently of
// `margin` (used for +Y/front and both X/side walls) -- defaults to
// `margin` so every existing call site keeps its old symmetric behavior
// unless it explicitly opts in. See rear_margin above for why this exists.
module main_footprint_2d(margin, rear = margin) {
    translate([-margin, -rear])
        offset(r = corner_r) offset(delta = -corner_r)
            square([board_w + 2*margin, board_d + margin + rear]);
}

module solid_from_footprint(margin, z0, z1, rear = margin) {
    translate([0,0,z0])
        linear_extrude(height = max(0.01, z1 - z0))
            main_footprint_2d(margin, rear);
}

// True 3D edge fillet on the TOP rim and the 4 vertical corners -- the
// BOTTOM edge (where the case meets the build plate) is now filleted too,
// per direction ("rounded bottom edges... wherever we meet the build
// plate... a 2mm rounding... all around the perimeter"), but NOT the same
// way as an earlier, failed attempt: that one used a full minkowski (all
// 12 edges + 8 corners), which is geometrically correct for a
// free-floating rounded box, but WRONG for this shell -- minkowski with a
// sphere tapers the cross-section down to nearly nothing right at the
// bottom plane (a sphere only touches a flat plane at a single point),
// which starved the FLOOR of full material near the edges and broke the
// CN3 collar's connection to the floor. This bottom fillet uses the SAME
// hull()-cap technique as the top one instead, just with its own (small,
// 2mm) radius -- the cross-section at z0 itself is inset by only br, not
// tapered to a point, and that inset is well clear of every interior
// feature's own clearance from the edge (case_margin/rear_margin, all
// >2mm) and fully resolved again by z0+br=2, well before the floor's own
// thickness (new_floor_t=2.4) even ends -- so nothing that actually
// attaches to the floor is affected, only the outer wall's own visible
// bottom edge. Opt-in (br defaults to 0, no bottom fillet) since the TOP
// shell also calls this same function with z0=parting_h -- that's the
// parting-line mating edge, not a build-plate surface, and must stay flat.
edge_fillet_r = 5;
bottom_fillet_r = 2;
module rounded_footprint_solid(margin, z0, z1, r = edge_fillet_r, rear = margin, br = 0) {
    union() {
        solid_from_footprint(margin, z0 + br, z1 - r, rear);
        hull() {
            translate([0, 0, z1 - r - 0.01])
                linear_extrude(0.01) main_footprint_2d(margin, rear);
            translate([0, 0, z1])
                linear_extrude(0.01) offset(delta = -r) main_footprint_2d(margin, rear);
        }
        if (br > 0)
            hull() {
                translate([0, 0, z0])
                    linear_extrude(0.01) offset(delta = -br) main_footprint_2d(margin, rear);
                translate([0, 0, z0 + br + 0.01])
                    linear_extrude(0.01) main_footprint_2d(margin, rear);
            }
    }
}

// Split into solid + hole so callers that need the pilot hole to survive
// being unioned with OTHER overlapping solid material (e.g. the cart
// support platform, which happens to sit right over a couple of these
// standoffs) can add the solid pegs in the union and cut all the holes in
// one later, outer difference() -- cutting the hole locally, inside this
// module, only works if nothing else solid gets unioned on top of it
// afterward, which is exactly what was silently filling some of them back
// in.
module standoff_peg_solid(x, y, hole_d, h, od = -1) {
    d = (od > 0) ? od : hole_d + 4.0; // od override for a deliberately thicker post
    translate([x, y, 0]) cylinder(d = d, h = h);
}
module standoff_peg_hole(x, y, hole_d, h) {
    translate([x, y, -0.5]) cylinder(d = hole_d - 0.2, h = h + 1); // self-tapping pilot
}
module standoff_peg(x, y, hole_d, h, od = -1) {
    difference() {
        standoff_peg_solid(x, y, hole_d, h, od);
        standoff_peg_hole(x, y, hole_d, h);
    }
}

module din_jack_cutout(d = 15.9, depth = 20) {
    // standard round panel-mount cutout, works for DIN-4/5/6/7/8 (shell OD standardized)
    rotate([-90,0,0]) cylinder(d = d, h = depth, center = false);
}

module rca_jack_cutout(d = 10.5, depth = 20) {
    rotate([-90,0,0]) cylinder(d = d, h = depth, center = false);
}

module rect_cutout(w, h, depth) {
    translate([-w/2, -depth/2, -h/2]) cube([w, depth, h]);
}

module cart_slot_cutout(w = 92, h = 13, depth = 20) {
    // standard 40-pos .1" edge-card envelope + margin; verify against real cart
    translate([-depth/2, -w/2, -h/2]) cube([depth, w, h]);
}

module louver_bank(n, slot_w, gap, run_len, cut_depth) {
    // n horizontal slots (elongated along X = run_len, thickness slot_w in Z),
    // stacked upward in Z, boring through in Y (cut_depth). Default
    // orientation suits a Y-facing wall (e.g. the rear panel); rotate the
    // whole call 90 deg about Z to bore an X-facing wall instead (e.g. the
    // left side panel) -- see main_louvers() for both uses.
    total = n*slot_w + (n-1)*gap;
    for (i = [0:n-1])
        translate([0, 0, -total/2 + i*(slot_w+gap)])
            translate([-run_len/2, -cut_depth/2, -slot_w/2])
                cube([run_len, cut_depth, slot_w]);
}

module louver_bank_vertical(n, slot_w, gap, run_len, cut_depth) {
    // Same idea as louver_bank(), but for a wall whose face normal is X
    // (the side walls): each slot runs VERTICALLY (long axis in Z, run_len
    // tall -- matching grooves that wrap DOWN from the roofline) and the n
    // slots are stacked along Y instead of Z. Bores through in X (cut_depth).
    total = n*slot_w + (n-1)*gap;
    for (i = [0:n-1])
        translate([0, -total/2 + i*(slot_w+gap), 0])
            translate([-cut_depth/2, -slot_w/2, -run_len/2])
                cube([cut_depth, slot_w, run_len]);
}

// ============================================================================
// MAIN (MOTHERBOARD) SHELL
// ============================================================================

/* [Keyboard shell -- from the hand-built "split key frame.scad"] */
kb_w = 334;            // overall width  (kx)
kb_d_key = 155;        // depth of the shell up to the keyboard's rear (the original frame's depth)
// kb_extra_d / kb_d (depth added BEHIND the keyboard) are derived further down, next to the
// board-A parameters they depend on -- kb_cap_h (below) does not depend on them, which is
// what lets the main case's skirt be derived from it up here.
kb_pocket_depth = 14.7;  // depth of the keyboard pocket: top surface above the pocket floor (vertical)
kb_raise = 3;          // the whole keyboard plane -- pocket floor AND top surface -- sits this much higher than the
                       // frame's original (front height 14.7 -> 14.7 + kb_raise). Each mm buys ~7mm of board headroom-depth
                       // at 8 deg, at the cost of 1mm of main-case tower (the skirt follows the keyboard, see kb_match_skirt).
kb_front_h = kb_pocket_depth + kb_raise;   // shell height at the FRONT edge (the "bottom front height")
kb_slope_deg = 8;      // keyboard-plane rise toward the back (15 was tried; 8 gets the overall height back)
kb_feet = one_piece_bottom;  // false: this shell sits directly on the desk (no stick-on feet), so its
                       // base plane is new_foot_height BELOW the main case's floor plane --
                       // lowers the whole keyboard relative to the main case's skirt.
                       // true (one_piece_bottom): on the same feet as the main case, one flat underside
kb_dz = kb_feet ? 0 : new_foot_height; // kb-frame z = main-frame z + kb_dz
kb_wall = 3;
kb_corner_r = 8;
kb_left_relief_extra = 4.5;  // the rectangular relief under the keyboard's left end (x 9..33) is this much deeper than the
                             // original frame's 3mm (fit testing: the stock keyboard needed it) -> 7.5 below the pocket floor
kb_floor_ovals = false;  // the four oval cut-outs in the floor from the original frame (vestigial -- no venting need); solid floor
                        // is stiffer in twist and keeps dust out, for ~30g
kb_base_t = 3;         // floor slab everywhere (was 5 under the hollows / 3 only under the board:
                       // the thinner deck under the PCB worked, so the whole floor is that now)
kb_pcb_w = 316;        // stock keyboard PCB pocket
kb_pocket_left_ext = 0.55;   // pocket extended this far LEFT: with its holes on the bezel-screw pattern the keyboard's 315.25
                             // outline sits 0.6 off-centre (8.77..324.02) and the 316 pocket (9..325) cut into it by 0.23
kb_pcb_d = 124;
kb_pocket_front_ext = 2.75;  // pocket extended this far FORWARD (only its front edge moves; the keyboard and screws don't):
                             // the keyboard sits 0.3 behind the original front edge and the OEM opening is nearly as deep as
                             // the keyboard, so the bezel had no front rail. 0.3 + 2.5 of bezel + 0.25 clearance.
kb_pocket_corner_r = 2.5;  // radius on the pocket's four corners (was square). NOTE: a stock PCB with square corners needs
                         // ~1.0mm of relief at each corner to seat (r*(sqrt2-1)) -- round/chamfer its corners, or set this to 0.
// The top stops rising here (flat shelf behind the keyboard) -- the height the
// shell would have had at its original depth, so kb_extra_d adds room, not height.
kb_cap_h = kb_front_h + tan(kb_slope_deg) * (kb_d_key - 2*kb_corner_r);
kb_x0 = board_w/2 - kb_w/2;   // main-frame X of the keyboard's left edge (centered on the main case)
kbpcb_screw_boss_h = 6; // was 3, raised per direction ("2 to 3 more mm height...
                         // for a bit more screw grab") -- still low/flush
                         // compared to the original 10mm freestanding pillar,
                         // just with more real self-tap thread engagement now.
// Board A (Pico, coco-keyboard -> USB), rotated 180deg from board B in the main case.
kbA_setback = kbpcb_edge_poke + 0.7;   // board's USB edge -> the inner face of the wall that sits AT the PCB's edge. The
                       // USB jack pokes 0.33mm past the edge, so this leaves 0.7mm to the jack.
// Layout along ky (front -> back):  ... keyboard pocket | board A (where headroom under the keyboard plane puts
// it) | 1mm | WALL (kb_wall) | CABLE BAY (kb_cable_bay_d, open at the back face toward the computer) |.
// The shell's roof carries on over the bay: that overhang hides the cable while docked, and the open bay gives
// the plug that sticks out of the main case's front wall somewhere to go as the keyboard is brought up.
kb_cable_bay_d = one_piece_bottom ? 8 : 12;   // depth of the bay behind the PCB-edge wall (was 20): needs a RIGHT-ANGLE / low-profile
                       // USB plug -- the plug-to-plug distance across the seam is kbA_setback + wall + this + the main case's
                       // wall/clearance (see the echo). One-piece: 8, to shorten the shelf; each plug then has ~13mm to the far wall.
kb_bay_x0 = kb_w/2 - fp_len/2;   // bay X extent = the shared faceplate window, centred on the header line (kx 97..237): it takes in A's
kb_bay_x1 = kb_w/2 + fp_len/2;   //   USB jack (kx ~126) and where board B's opening lands in this frame (kx ~198..218), ~81mm apart
kbA_flipped = false;   // true: board mounted UPSIDE DOWN (components hang below the PCB, bare
                       // face up) -> almost no headroom needed under the keyboard, but the
                       // bay needs depth below the PCB instead (see the echo() lines)
kbA_flip_pcb_z = kb_base_t + kbpcb_comp_above + 0.5;   // PCB height when flipped: real component depth (8.6) + clearance
kbA_floor_z = kb_base_t; // bay floor == the general floor now (3mm)
kbA_pcb_z = kbA_flipped ? kbA_flip_pcb_z : kbpcb_screw_boss_h; // PCB slab bottom above the shell
                       // base plane (upright default 6 = board B's height above the main floor)
kb_usb_w = 20; kb_usb_h = 11; // same opening size as main_usb_passthrough_front()
// Headroom the board needs under the keyboard PCB plane (whose height above the base at the board's front
// edge is ky*tan(slope)): the PCB plus whatever stands on it (upright: the tallest header; flipped: only a
// screw head). It sets how far back the board sits (kbA_edge_ky, below) -- shallower slopes push it back.
// Board A's back (USB) edge: the board sits under the keyboard plane, whose height above the base at the board's
// FRONT edge is ky*tan(slope). That front edge has to be far enough back to clear the PCB plus the tallest part
// (upright: the real 8.62mm headers; flipped: only a screw head) -- so shallower slopes push the board back.
// Never further forward than the original frame's rear rim (kb_d_key - kb_wall - kbA_setback).
// Each tall part only needs the keyboard plane to clear IT, at ITS distance behind the board's front edge -- not the
// whole board at the front edge. [ly of the part's front-most point, its height above the PCB top], from the
// stuffed-board STL. The frontmost 1x16 header footprint is NOT populated, so it is not listed; if it ever is, add it.
kbA_parts = [ [0, 0],            // the bare PCB
              [18.53, 3.58],     // Pico
              [19.37, 8.62],     // the installed 1x16 header (the tallest, and the front-most tall part)
              [33.47, 8.62],     // 1x4 header
              [50.23, 8.62],     // 2x5 header (J6)
              [53.20, 8.62],     // 1x2 header
              [62.28, 8.38],     // LED lenses
              [62.85, 7.09] ];   // button
function kbA_ylo_min() = kbA_flipped
    ? (kbA_pcb_z + kbpcb_thickness + 3 - kb_raise) / tan(kb_slope_deg)          // flipped: only a screw head stands up
    : max([ for (c = kbA_parts) (kbA_pcb_z + kbpcb_thickness + c[1] + 0.9 - kb_raise) / tan(kb_slope_deg) - c[0] ]);
kbA_edge_ky = max(ceil(kbA_ylo_min()) + kbpcb_d, kb_d_key - kb_wall - kbA_setback);
kbA_wall_y0 = kbA_edge_ky + kbA_setback;      // inner face of the PCB-edge wall
kbA_wall_y1 = kbA_wall_y0 + kb_wall;          // its back face = start of the cable bay
kb_d = kbA_wall_y1 + kb_cable_bay_d;          // overall depth (ky)
kb_extra_d = kb_d - kb_d_key;
kb_rear_h = kb_front_h + tan(kb_slope_deg) * (kb_d - 2*kb_corner_r);   // plane height at the rear cylinders (cutting height)
// Height of the keyboard's top at its back face (what the main case's front skirt meets). Normally the top stops rising
// at kb_cap_h and runs back flat (the shelf). One-piece: no flat shelf -- the keyboard plane carries on at kb_slope_deg
// right to the back face, so it flows straight into the main top's ramp (the tower rises with it).
kb_back_h = one_piece_bottom ? kb_front_h + tan(kb_slope_deg) * kb_d : kb_cap_h;
// The main case's front skirt is derived from the keyboard: the keyboard's flat shelf top
// (kb_cap_h, measured from ITS base = kb_dz below the main floor) meets the main case's
// front skirt top flush. The floppy-bay stack rises by the same amount (see bay_face_z0)
// so the ramp run and every bay Y position stay exactly as they were.
kb_match_skirt = true;

// ---- TOP SHELL STYLING: skirt + continuous slope, no flat "table" ----
// Per direction: the front has NO flat plateau -- a short vertical "skirt"
// (15-20mm) right where the top shell meets the bottom shell's parting
// line, then the roof climbs continuously at a fixed angle all the way back
// to the tall tower. The tower's own height is driven by what it actually
// needs to hold -- two side-by-side 3.5" floppy bays (see FLOPPY BAY below)
// -- not an arbitrary styling constant like the old front_deck_h/
// rear_tower_h were.
top_skirt_h_base = 8;
top_skirt_h   = kb_match_skirt ? (kb_back_h - kb_dz - parting_h) : top_skirt_h_base;
                      // ^ was a flat 8: now matches the keyboard shell's flat shelf top (kb_match_skirt).
                      // Vertical wall height above parting_h at the front edge -- reduced
                        // from 18 per direction ("straight up band interface to the base...
                        // can be reduced to 8mm")
top_slope_deg = 25;   // front-to-back roof slope, measured from VERTICAL per
                        // direction (NOT from horizontal) -- so this is a steep,
                        // near-vertical rise leaning back only 25 deg, not a
                        // gentle ramp. run = rise * tan(top_slope_deg), the
                        // opposite of the usual rise/tan(angle)-from-horizontal
                        // formula -- see top_ramp_run below.

// ---- FLOPPY BAY (2x, side by side, 3.5" front-loading from the tower's
// user-facing side, per direction) ----
// Real drive envelope -- a standard 3.5" floppy drive, NOT a distinct
// "half-height" 3.5" SKU (those aren't a commodity part the way half-height
// 5.25" drives were) -- PLACEHOLDER data (see CLAUDE.md's own PLACEHOLDER
// section) until checked against a real drive's datasheet.
floppy_w            = 101.6;
floppy_h            = 25.4;
floppy_d            = 120;   // real drive depth -- per direction, the specific part in mind
                               // is a Gotek drive emulator (~120mm deep), not a real
                               // full-depth 3.5" FDD; the tower now has ~137mm of
                               // available depth behind the bay face (see
                               // main_floppy_bay_brackets()), comfortably enough.
// Per-axis clearance added to the through-opening. A real print came back
// "about 3mm too wide and 2mm too tall" against the actual drive, so this
// replaces the old single floppy_fit_clear=3 (applied to both axes) --
// width clearance is now essentially zero (0.3mm, not a hard zero, so
// there's still SOME slip fit rather than a knife-edge tolerance) and
// height barely more than a friction fit. Worth confirming against the
// physical drive before committing another full print -- FDM holes often
// print a touch undersized, so this may still need easing.
floppy_fit_clear_w = 0.3;
floppy_fit_clear_h = 1.3;
floppy_bay_gap      = 20;    // divider width between the two bays -- widened from 10
                               // per direction ("a bit more separation between the bays")
floppy_bay_margin   = 20;    // decorative surround margin around the bay PAIR, LEFT/RIGHT only
floppy_bay_margin_v = 8;     // surround margin, TOP/BOTTOM -- kept much smaller than the L/R
                               // margin per direction ("much taller than it needs to be" --
                               // 20mm top AND bottom around a 25.4mm-tall opening was most
                               // of what drove the tower height, not anything structural)
floppy_face_w = 2*floppy_w + floppy_bay_gap + 2*floppy_bay_margin;
floppy_face_h = floppy_h + 2*floppy_bay_margin_v;

// Standard 3.5" drive side-mounting screw positions, measured from the
// drive's own FRONT bezel plane. REAL measurements off the user's own
// Gotek (front edge of each hole, per spec): 20mm and 79.2mm -- those are
// to the NEAR edge of the hole, not its center, so the screw-hole radius
// is added to get the true center offset used below. (Previous [12, 92]
// values were unverified placeholders and measured ~13-14mm off in
// practice -- confirmed by a real print: the drive stuck out that much
// when mounted through these holes.)
floppy_screw_front_offsets = [20 + m3_pilot_d/2, 79.2 + m3_pilot_d/2];
// Z height of the screw holes, up from the drive's own bottom edge. The
// generic 3.5"/floppy spec position is 12.7mm; the user's particular
// Gotek unit instead has its holes at 4.2mm. Drilling both lets either
// mount without forcing a specific drive.
floppy_screw_z_offsets = [4.2, 12.7];

// ---- Tower height, driven by the bay stack (not picked by hand) ----
bay_face_z0  = parting_h + 6 + 19.05 + (top_skirt_h - top_skirt_h_base); // rises with the skirt    // footer below the recessed face -- includes an
                                           // extra 3/4in (19.05mm) of clearance underneath
                                           // the bays per direction (was just 6mm); this
                                           // raises the whole bay assembly, and rear_tower_h
                                           // with it, since rear_tower_h is still derived
                                           // from bay_face_z0 + floppy_face_h + roof margin
bay_face_z1  = bay_face_z0 + floppy_face_h;
rear_tower_h = bay_face_z1 + 8;          // + roof clearance above the bays
// The drive openings' bottom edge, projected back as a horizontal plane: the drive screw-hole heights
// (floppy_screw_z_offsets) are measured up from THIS line, not from the surround's bottom edge (bay_face_z0).
floppy_opening_z0 = bay_face_z0 + floppy_bay_margin_v - floppy_fit_clear_h/2;
// Drive brackets now stop just below the lowest screw hole (was: all the way down to bay_face_z0), with rounded free corners.
floppy_rail_hole_margin = 6;                                              // lowest hole centre -> rail's bottom edge
floppy_rail_corner_r    = 4;                                              // radius on the rail's free corners
floppy_rail_z0 = floppy_opening_z0 + min(floppy_screw_z_offsets) - floppy_rail_hole_margin;
front_deck_h = parting_h + top_skirt_h;  // front wall height (the "skirt")

// Ramp run needed to climb from the front skirt to the tower height at
// top_slope_deg -- this, not an arbitrary fraction of the case depth (the
// old rear_break_front/rear_break_back), is what determines where the flat
// tower actually begins. top_slope_deg is measured from VERTICAL (per
// direction), so run = rise * tan(angle) here, not rise / tan(angle).
top_ramp_run   = (rear_tower_h - front_deck_h) * tan(top_slope_deg);
top_front_wall_y = board_d + case_margin; // same value as main_front_y (defined
                                            // later) -- recomputed here since
                                            // top-level plain expressions
                                            // evaluate in file order, and
                                            // main_front_y isn't assigned yet
                                            // at this point in the file.

main_depth = board_d + case_margin + rear_margin;
main_break2_y = top_front_wall_y;         // no flat front section at all -- the ramp
                                            // runs straight to the front wall itself
main_break1_y = max(main_break2_y - top_ramp_run, 5); // clamped so it can never go
                                                          // negative/degenerate if the
                                                          // ramp run ever exceeds the
                                                          // available depth

// Shared Y positions for the wrap-around groove pattern (see
// main_louvers(), which builds the whole continuous side-corner-top sweep
// per groove_y).
function groove_y_positions(n, slot_w, gap, center_y) =
    let(total = n*slot_w + (n-1)*gap)
    [for (i = [0:n-1]) center_y - total/2 + i*(slot_w+gap)];
groove_pitch = louver_w + louver_gap;
groove_span = main_break1_y * 0.95; // per direction: "3 or four more" grooves,
                                       // continuing across the top and around to
                                       // the other side -- wider span than before
groove_count = max(1, min(louver_count, floor((groove_span + louver_gap) / groove_pitch))) + 4;
groove_center_y = main_break1_y / 2;
groove_ys = groove_y_positions(groove_count, louver_w, louver_gap, groove_center_y);

// Y=0 is the REAR (connector) edge, so the tall louvered tower -- which
// houses the rear panel and, per the reference photo, sits at the BACK of
// the machine -- is clipped to LOW Y. The low front deck (keyboard side)
// is clipped to HIGH Y.
//
// IMPORTANT: do NOT hull() the whole board footprint against itself to loft
// the wedge -- the board outline is concave (tab + relief notches) and
// hull() convexifies everything it touches, which is what turned this into
// a smooth curved boat hull instead of a case. Instead: extrude the REAL
// (non-convex) outline straight up to full height, and separately clip that
// extrusion's height as a function of Y only, using a wedge block built from
// two axis-aligned boxes that share the same X range -- hull() of those two
// stays a clean flat-flat-ramp profile because there's no X variation for it
// to convexify.
// The wedge's outer roofline height as a function of Y alone -- flat at
// h_rear for y <= break1, flat at h_front for y >= break2, straight ramp
// between. Used to size anything that needs to reach from the parting-line
// rim up to the actual roof at a given Y (e.g. the top/bottom screw bosses).
function local_wedge_h(y, h_rear, h_front) =
    (y <= main_break1_y) ? h_rear :
    (y >= main_break2_y) ? h_front :
    h_rear + (h_front - h_rear) * (y - main_break1_y) / (main_break2_y - main_break1_y);

module y_wedge_block(x0, x1, h_rear, h_front) {
    // The rear/front boxes must start well before the footprint's actual
    // outer edges (-rear_margin at the rear, main_depth+case_margin at the
    // front) or this block has NO material in the gap, silently deleting
    // whatever it's intersected with there -- a +/-1mm margin here (this
    // bug's previous value) is not generous enough once case_margin=6 is
    // taken into account, and it deleted the entire rear wall face.
    //
    // BUT: that front-side margin must NOT be part of the hull() that forms
    // the ramp, or the ramp stops being "flat-ramp-flat" at all. hull()ing
    // the rear box directly against the (far-extended) front box makes the
    // hull's own convex boundary run from the rear box's top corner
    // (main_break1_y, h_rear) all the way to the FRONT box's FAR corner
    // (main_depth+margin, h_front) -- the front box's NEAR corner (right at
    // main_break2_y, where the ramp is supposed to end) sits strictly below
    // that straight line and never becomes a hull vertex, so the "ramp"
    // silently drags on almost to the outer front wall instead of ending at
    // main_break2_y like local_wedge_h() (used everywhere else to size
    // features against this same roofline, e.g. the top/bottom screw bosses)
    // assumes. Caught via a disconnected boss: local_wedge_h() said the roof
    // was already down at h_front by the boss's Y, but the real roof there
    // was still ~11mm higher mid-ramp, so the boss fell short of it.
    // Fix: hull() only the rear box against a paper-thin anchor slice
    // sitting exactly at main_break2_y (so the ramp really ends there), then
    // union() in the far-extended flat front box separately -- it still
    // reaches past the real front wall, but as a plain flat slab, not a
    // hull() operand that can bend the ramp's endpoint.
    margin = 50;
    union() {
        hull() {
            translate([x0, -margin, 0]) cube([x1-x0, main_break1_y+margin, max(h_rear, 0.01)]);
            translate([x0, main_break2_y, 0]) cube([x1-x0, 0.01, max(h_front, 0.01)]);
        }
        translate([x0, main_break2_y, 0]) cube([x1-x0, (main_depth-main_break2_y)+margin, max(h_front, 0.01)]);
    }
}

// ---- BOTTOM shell: a plain shallow tray up to parting_h, flat, no wedge --
// per a photo of a real stock case bottom (floor, standoffs, no connector
// cutouts, no styling). Much simpler than the wedge: just the rounded-rect
// footprint, extruded straight up.
module main_bottom_outer_solid() {
    // r=0: the bottom shell's own TOP edge (Z=parting_h, where it meets
    // the top shell's parting line) must stay a plain flat/sharp wall, not
    // rounded_footprint_solid()'s default top-edge treatment (edge_fillet_r
    // = 5mm) -- per direction, that top edge is a deliberate ~1.6mm
    // vertical lip above the standoff height (parting_h = standoff_height
    // + pcb_edge_lip_height), and a 5mm chamfer completely swallows a
    // feature that short, replacing it with what reads as a bevel instead
    // of the intended lip ("too short... has a 45deg inward bevel").
    // br=bottom_fillet_r (2mm) is unaffected -- that's the OTHER end
    // (Z=0, the build plate), a separate, deliberately-requested fillet.
    rounded_footprint_solid(case_margin, 0, parting_h, r = 0, rear = rear_margin, br = bottom_fillet_r);
}
module main_bottom_inner_cavity() {
    // open at the top rim (pokes through by 5mm so there's no ceiling)
    solid_from_footprint(case_margin - wall, new_floor_t, parting_h + 5, rear = rear_margin - wall);
}

// ---- TOP shell: the styled wedge (tower/ramp/deck + louvers), spanning
// from parting_h up to the roofline. Same footprint-extrude +
// height-clipping-wedge-block technique as before, just z-shifted to start
// at parting_h instead of 0.
// Rounds a single straight OUTER (convex) edge -- where a vertical wall
// meets the flat top -- with a TRUE quarter-circle fillet, not the
// chamfer the hull()-between-two-flat-slabs technique (rounded_footprint_
// solid's own top cap, used elsewhere) actually produces: hull() of two
// parallel flat plates at different heights/insets tapers LINEARLY between
// them, which is a 45-degree-ish bevel, confirmed by rendering a cross-
// section -- not the curved "5mm radius" round asked for here. This uses
// the standard notch-cut-plus-cylinder construction instead: within the
// r x r square where the sharp corner would be, subtracting a cylinder
// (radius r, axis along the edge's own run direction) from that square
// leaves exactly the sharp sliver beyond the round; subtracting THAT
// sliver from the box leaves a true quarter-circle profile.
// round_edge_over: every cut below used to box exactly up to the material's own outer faces (X=wall, Z=z1) -- a
// textbook degenerate-CSG coincident-face situation (same class already flagged elsewhere in this file, e.g. the
// "Padded 2mm" note on main_top_outer_solid), and the actual cause of the non-manifold edges Bambu Studio was
// flagging: confirmed by isolating a single groove position and the outer solid together, then tracing the exact
// duplicated triangle to this cut's own box, present even with every groove disabled (a small pre-existing baseline
// the grooves then multiplied wherever they crossed the same coincident line). Overshooting the box's own OUTER faces
// (the ones that aren't part of the visible rounded profile) by this amount gives real volume overlap instead.
round_edge_over = 1;
module round_top_edge_x(edge_y, r, x0, x1, z1) {
    // Edge running along X, where Z=z1 (top) meets Y=edge_y (a wall),
    // material at Y > edge_y.
    over = round_edge_over;
    difference() {
        translate([x0, edge_y - over, z1-r]) cube([x1-x0, r + over, r + over]);
        translate([x0, edge_y+r, z1-r]) rotate([0,90,0]) cylinder(r=r, h=x1-x0);
    }
}
module round_top_edge_y(edge_x, dir, r, y0, y1, z1) {
    // Edge running along Y, where Z=z1 (top) meets X=edge_x (a wall).
    // dir=-1: material at X < edge_x (a max-X wall); dir=+1: material at
    // X > edge_x (a min-X wall).
    cx = edge_x + dir*r;
    over = round_edge_over;
    x0 = dir > 0 ? edge_x - over : edge_x - r;
    x1 = dir > 0 ? edge_x + r    : edge_x + over;
    difference() {
        translate([x0, y0, z1-r]) cube([x1 - x0, y1-y0, r + over]);
        translate([cx, y0, z1-r]) rotate([-90,0,0]) cylinder(r=r, h=y1-y0);
    }
}
module main_top_edge_round_cut() {
    // Per direction: round the top-back/top-left/top-right edges (NOT
    // top-front, which is the sloped ramp -- there's no sharp horizontal
    // edge there to round) with a 5mm radius. Y-range for the left/right
    // edges overshoots slightly past main_break1_y (the flat tower's own
    // front extent); harmless, since the wedge is already well below
    // z1-r there and this cut has nothing to remove past that point.
    r = edge_fillet_r;
    z1 = rear_tower_h;
    min_x = -case_margin;
    max_x = board_w + case_margin;
    x_span0 = min_x - 1;
    x_span1 = max_x + 1;
    y0 = -rear_margin - 1;
    y1 = main_break1_y + 1;
    round_top_edge_x(-rear_margin, r, x_span0, x_span1, z1);
    round_top_edge_y(max_x, -1, r, y0, y1, z1);
    round_top_edge_y(min_x, 1, r, y0, y1, z1);

    // The two straight-edge cuts above overlap imperfectly right where the back edge meets each side edge (independent
    // circular cuts, not a true compound 3D fillet). Since corner_r and edge_fillet_r are conveniently the same 5mm,
    // this compound corner is exactly a spherical octant: same notch-minus-primitive technique as the straight edges,
    // just with a sphere instead of a cylinder, cleanly covering both cuts' overlap. Overshoots ALL SIX faces by
    // round_edge_over: not just the three that land on the material's own outer surface, but also the two (at
    // min_x+r / max_x-r) that land exactly on round_top_edge_y's OWN cut boundary right next door -- two different
    // subtractions meeting at an exact shared plane is the same degenerate situation, just cut-vs-cut instead of
    // cut-vs-material.
    over = round_edge_over;
    difference() {
        translate([min_x - over, -rear_margin - over, z1-r-over]) cube([r + 2*over, r + over, r + 2*over]);
        translate([min_x+r, -rear_margin+r, z1-r]) sphere(r=r);
    }
    difference() {
        translate([max_x-r-over, -rear_margin - over, z1-r-over]) cube([r + 2*over, r + over, r + 2*over]);
        translate([max_x-r, -rear_margin+r, z1-r]) sphere(r=r);
    }
}

// Mirror of round_top_edge_x, for a wall where material/cavity is on the
// Y < edge_y side instead of Y > edge_y (the front wall, where the
// interior extends toward the REAR from there).
module round_top_edge_x_neg(edge_y, r, x0, x1, z1) {
    difference() {
        translate([x0, edge_y-r, z1-r]) cube([x1-x0, r, r]);
        translate([x0, edge_y-r, z1-r]) rotate([0,90,0]) cylinder(r=r, h=x1-x0);
    }
}

// Small STRUCTURAL fillet at the INSIDE corner where the ceiling meets
// the walls, all the way around -- per direction. Same notch-cube-minus-
// cylinder technique as main_top_edge_round_cut() above (a true round,
// not the hull()-based chamfer used elsewhere), just applied the other
// way: this shape gets SUBTRACTED FROM THE CAVITY (see its use in
// main_case_top(), added to the same protection union that already keeps
// the floppy duct/roof-fill and topbottom boss footprints solid) rather
// than from the outer solid, so removing it from the cavity is what
// LEAVES the fillet's own material behind in the final shell -- the
// opposite of cutting a fillet into already-solid material.
//
// The rear and front walls are each flat (a single z1 applies along
// their whole run), but the side walls' own ceiling height follows the
// sloped ramp -- swept in many small segments using local_wedge_h() at
// each one (same principle as the corner boss's own slope-following
// construction), staying purely algebraic to avoid the CGAL mesh-
// robustness issues a real geometry intersection would risk here.
ceiling_fillet_r = 3;
module round_ceiling_edge_y_swept(edge_x, dir, r, y0, y1, h_rear, h_front, n = 100) {
    step = (y1 - y0) / n;
    for (i = [0 : n-1]) {
        ys = y0 + i*step;
        ye = ys + step + 1; // generous overlap between segments for a clean union
        ym = ys + step/2;
        z1 = local_wedge_h(ym, h_rear, h_front);
        round_top_edge_y(edge_x, dir, r, ys, ye, z1);
    }
}
module main_ceiling_fillet_protect() {
    r = ceiling_fillet_r;
    right_inner_x = -(case_margin - wall);
    left_inner_x  = board_w + (case_margin - wall);
    rear_inner_y  = -(rear_margin - wall);
    front_inner_y = main_front_y - wall;
    ceil_rear  = rear_tower_h - wall;
    ceil_front = front_deck_h - wall;
    // rear wall -- flat, entirely within the flat-roof zone
    round_top_edge_x(rear_inner_y, r, right_inner_x - r, left_inner_x + r, ceil_rear);
    // front wall -- flat at the skirt's own height
    round_top_edge_x_neg(front_inner_y, r, right_inner_x - r, left_inner_x + r, ceil_front);
    // side walls -- swept the full length, following the ramp's own slope
    round_ceiling_edge_y_swept(right_inner_x, 1, r, rear_inner_y - r, front_inner_y + r, ceil_rear, ceil_front);
    round_ceiling_edge_y_swept(left_inner_x, -1, r, rear_inner_y - r, front_inner_y + r, ceil_rear, ceil_front);
}

module main_top_outer_solid() {
    // Padded 2mm above the wedge block's own max height so the two solids
    // being intersected never share an exactly coincident flat top plane --
    // see main_bottom/top_inner_cavity below for why that matters (CGAL
    // treats an exact coincidence as degenerate and renders visible sliver
    // artifacts).
    difference() {
        intersection() {
            solid_from_footprint(case_margin, parting_h, max(rear_tower_h, front_deck_h) + 2, rear = rear_margin);
            y_wedge_block(-500, board_w+500, rear_tower_h, front_deck_h);
        }
        main_top_edge_round_cut();
    }
}
module main_top_inner_cavity() {
    // Inset by `wall` in XY; open at the BOTTOM rim (pokes through below
    // parting_h so it mates with the open-top bottom tray) and capped with
    // a proper `wall`-thick roof at the top this time (unlike the bottom
    // tray, the top shell actually needs a ceiling).
    extra = 5;
    intersection() {
        solid_from_footprint(case_margin - wall, parting_h - extra, max(rear_tower_h, front_deck_h) - wall + 2, rear = rear_margin - wall);
        y_wedge_block(-500, board_w+500, rear_tower_h - wall, front_deck_h - wall);
    }
}

// ---- Groove geometry: half-round profile, continuous/unbroken across the
// newly-rounded top corner -- per direction ("the groove should be half
// round, as if a half cylinder was removed" + "continuous/unbroken...
// across that radius"). A cylinder (or, along the curved corner, a chain
// of hulled spheres) with its axis running ALONG the groove's own path and
// positioned exactly AT the material's outer surface only ever removes the
// "inward half" of its own cross-section -- the other half is in open air
// -- which is exactly a half-round channel; sweeping that same radius
// along the whole path (straight side wall -> the 5mm corner arc ->
// straight top) keeps it visually unbroken the whole way around.
groove_r = louver_w / 2;

module groove_vertical_side(wall_x, dir, y, z0, z1, through_depth) {
    // Half-round entry (cylinder axis along Z, at the wall's own outer
    // surface) + a plain straight continuation so it actually penetrates
    // the full wall thickness for ventilation -- the half-round alone
    // (depth = groove_r) can't reach through a case_margin-thick wall.
    // z1 is exactly where the corner sweep's own arc starts (see side_vent_z1) -- extending a hair past it (same
    // round_edge_over idea as the top-edge rounding cuts) gives genuine overlap there instead of a tangent touch.
    // z0 (this cut's own bottom cap) also used to land flush with the wall's outer surface at an otherwise unrelated
    // Z, which was leaving the same kind of coincident-face artifact -- overshot by the same margin below.
    x_start = dir > 0 ? wall_x : wall_x - through_depth;
    z0e = z0 - round_edge_over;
    zh = (z1 + round_edge_over) - z0e;
    union() {
        translate([wall_x, y, z0e]) cylinder(r = groove_r, h = zh);
        translate([x_start, y - groove_r, z0e])
            cube([through_depth, groove_r*2, zh]);
    }
}

// Was a chain of hulled sphere-pairs along the sampled arc: adjacent segments shared EXACTLY one sphere at their
// common endpoint -- a knife-edge touch, not real volume overlap -- which left a degenerate coincident face at every
// one of those junctions (confirmed: disabling just this sweep dropped main_top_right's non-manifold edge count from
// ~1300 to 125; padding the segments to overlap didn't help, it just moved the seams). A torus segment -- one true
// rotate_extrude, no internal seams at all -- is what the shape actually is (a round tube of radius groove_r, swept
// along the same arc as the case's own edge fillet), so build it as one directly instead.
module groove_corner_sweep(cx, cz, R, theta0, theta1, y) {
    translate([cx, y, cz]) rotate([90, 0, 0]) rotate([0, 0, theta0])
        rotate_extrude(angle = theta1 - theta0, $fn = 96)
            translate([R, 0]) circle(r = groove_r, $fn = 24);
}

module groove_horizontal_top(z, y, x0, x1) {
    translate([x0, y, z]) rotate([0,90,0]) cylinder(r = groove_r, h = x1 - x0);
}

module main_louvers() {
    // Vents go on the left/right side walls only -- per direction, no
    // vents on the back wall. Only the portion of the tower that's part of
    // the TOP shell (parting_h..rear_tower_h) is available for the bank.
    min_x = -case_margin;
    max_x = board_w + case_margin;
    r = edge_fillet_r; // matches the top-edge rounding radius exactly, so the
                         // corner sweep below follows the SAME arc as the case's
                         // own rounded edge -- true continuity, not an approximation
    side_vent_z0_base = max(41.85 + 2, parting_h + 6);
    // min-X wall also carries the CN1 cart slot (a much taller cutout than
    // the rear connector notches, per direction it's now 108x23 real size
    // + margin) -- side_vent_z0_base only cleared the REAR connectors'
    // height, not this. The vertical grooves' own bottom end was starting
    // BELOW the cart slot's own top, cutting straight through/into ground
    // the cart slot already opened up -- unprintable per direction ("the
    // vent cuts on the right just go all the way to the cart cutout").
    // Raised 8mm clear of the cart slot's own top, min-X wall only; max-X
    // (no cart slot) keeps the lower, unrestricted floor.
    cart_slot_top_z = parting_h + cart_slot_h + cart_slot_margin_h;
    min_x_vent_z0 = max(side_vent_z0_base, cart_slot_top_z + 8);
    max_x_vent_z0 = side_vent_z0_base;
    side_vent_z1 = rear_tower_h - r; // stop right where the corner arc begins
    top_x0 = min_x + r; // where the top groove begins, past the left corner arc
    top_x1 = max_x - r; // where the top groove ends, before the right corner arc

    for (y = groove_ys) {
        groove_vertical_side(min_x, 1, y, min_x_vent_z0, side_vent_z1, louver_depth*4);
        groove_vertical_side(max_x, -1, y, max_x_vent_z0, side_vent_z1, louver_depth*4);
        groove_corner_sweep(min_x + r, rear_tower_h - r, r, 180, 90, y);
        groove_corner_sweep(max_x - r, rear_tower_h - r, r, 0, 90, y);
        groove_horizontal_top(rear_tower_h, y, top_x0, top_x1);
    }
}

// U-shaped notches open at the TOP shell's own bottom rim (parting_h),
// rising `height` above it -- per a photo of a real stock case, which cuts
// all its connector-panel openings in the TOP shell, not the bottom. This
// also happens to be far more printable than a fully-enclosed round hole
// mid-wall: printed upside down (rim facing up on the bed), each notch is
// just an open channel with zero overhang, no supports needed. Sizes are
// still the same placeholder commodity-connector envelopes flagged in the
// file header -- only the shape (closed hole -> open notch) changed here.
module rim_notch_y(x, wall_y, width, height, depth, r = 0) {
    // r > 0: rounded-corner cutout (per direction, "round them off a bit"),
    // reusing the same rounded_rect_prism_y() helper the floppy bay notch
    // uses. r = 0 (default): the original sharp-cornered cutout.
    if (r > 0)
        rounded_rect_prism_y(x - width/2, x + width/2, parting_h - 1, parting_h + height, wall_y, wall_y + depth, r);
    else
        translate([x - width/2, wall_y, parting_h - 1])
            cube([width, depth, height + 1]);
}
module rim_notch_x(wall_x, y, width, height, depth, dir = -1, taper = 0, taper_grow = 0) {
    // dir=-1: wall_x is a max-X (right, in the old pre-mirror sense) wall,
    //         cut inward toward -X.
    // dir=+1: wall_x is a min-X wall, cut inward toward +X. Cart slot uses
    //         this now that it's on the min-X wall (post board_pt mirror).
    // taper > 0: flares the opening at the wall's own OUTER face, wider by
    //            taper_grow (total, split across width and height) right
    //            at the surface, narrowing back down to the nominal
    //            width x height over a `taper` mm run -- a lead-in funnel
    //            to help guide something into the slot by feel.
    x0 = (dir < 0) ? wall_x - depth : wall_x;
    if (taper > 0) {
        x_in = (dir < 0) ? wall_x - taper : wall_x + taper; // taper's inward (nominal-size) end
        outer_off = (dir < 0) ? -0.01 : 0;
        inner_off = (dir < 0) ? -0.01 : 0;
        hull() {
            translate([wall_x + outer_off, y - (width+taper_grow)/2, parting_h - 1])
                cube([0.01, width+taper_grow, height+taper_grow+1]);
            translate([x_in + inner_off, y - width/2, parting_h - 1])
                cube([0.01, width, height + 1]);
        }
    }
    translate([x0, y - width/2, parting_h - 1])
        cube([depth, width, height + 1]);
}

// Rear-panel USB-C power input -- replaces the OEM power header (out of
// scope to reuse, see file header). Position along the rear wall is a
// placeholder: parked left of SW1 in open space, clear of every real
// connector; move it once you've picked an actual USB-C panel-mount part.
//
// Cutout disabled per direction (see its own commented-out call in
// main_connector_cutouts_top() below) -- kept overlapping the right-rear
// topbottom screw boss area even after moving it, and with no real part
// picked yet there's no reason to keep chasing a placeholder hole's exact
// position. usbc_power_x is unused while that's commented out; re-enable
// both once a real USB-C panel-mount part is chosen.
usbc_power_x = 5;

// Separate USB-C PD "trigger" board mount, back-left corner (per
// direction) -- clear of SW1 (the leftmost real rear connector, X~232) --
// so the board can be installed and powered with the case closed and
// nothing else populated yet; the trigger board's own USB-C port is
// accessible through this rear cutout, and everything else it needs
// (buttons, LEDs, output pads) lives on the board itself. First-pass
// generic dimensions -- common small USB-C PD trigger boards run around
// 22x22mm -- true up once you've picked the real part.
usbc_trigger_x        = 264; // moved 8mm right (was 272) -- the left-rear topbottom screw
                               // boss was nudged further in (see main_topbottom_screw_rf_inset)
                               // and its 10mm footprint now reaches to X~279, which the
                               // board's old position (span 261-283) overlapped
usbc_trigger_cut_w     = 14; // rear cutout for the USB-C port + cable clearance
usbc_trigger_cut_h     = 7;
usbc_trigger_board_w   = 22;
usbc_trigger_board_d   = 22;
// The real USB-C power board (no mounting holes): PCB 16.2 x 10.6 x 1.6, a TOP-MOUNT USB-C receptacle on one short edge
// overhanging the PCB by 1.3 (17.5 overall), the power cable soldered through-hole ~1mm in from the opposite edge. It
// sits in usbc_clip() (part "usbc_clip"), a small plate screwed onto the four bosses below -- the board is 10.6 wide and
// the gap between the bosses only ~9.4, so it rides on top of them -- and the rear cutout is centred on its port.
usbc_pcb_w      = 10.6;
usbc_pcb_l      = 16.2;
usbc_pcb_t      = 1.6;
usbc_conn_over  = 17.5 - 16.2;   // receptacle past the PCB edge
usbc_conn_h     = 3.2;           // receptacle height (typical); its centre sets the cutout height
usbc_clip_t     = 3.2;           // plate thickness (M3 pan/button heads sink into it)
usbc_trigger_boss_h    = 6;  // was 3, raised +3mm per direction ("raised about 3mm
                              // including taller standoff so I get better screw
                              // grabbing... self tapping m3 is fine for that in all
                              // conditions") -- same reasoning/precedent as the kbpcb
                              // boss height increase above.
usbc_trigger_hole_d    = m3_pilot_d; // self-tapping M3 confirmed fine here, per direction
usbc_trigger_cut_z     = 6;  // cutout vertical center above the floor
// NOTE: on usbc_clip() the port centre is at usbc_trigger_boss_h + usbc_clip_t + usbc_pcb_t + usbc_conn_h/2 (12.4), not
// here -- the bottom is deliberately left as is until the clip is test-fitted.
module main_usbc_trigger_cutout() {
    // Through the (bottom-shell) rear wall, at floor level -- the board
    // sits on its own low bosses (usbc_trigger_boss_h) just inside, so its
    // port lines up here rather than up at parting_h like the panel
    // notches in main_connector_cutouts_top() (those are TOP-shell, cut
    // relative to the parting line; this board is a BOTTOM-shell floor
    // feature, so it needs its own cut through this wall instead).
    translate([usbc_trigger_x - usbc_trigger_cut_w/2, -rear_margin - 1, usbc_trigger_cut_z - usbc_trigger_cut_h/2])
        cube([usbc_trigger_cut_w, rear_margin + 2, usbc_trigger_cut_h]);
}
module main_usbc_trigger_standoffs_solid() {
    inner_wall_y = -(rear_margin - wall);
    for (dx = [-1, 1])
        translate([usbc_trigger_x + dx*(usbc_trigger_board_w/2 - 3), inner_wall_y + 3, 0])
            standoff_peg_solid(0, 0, usbc_trigger_hole_d, usbc_trigger_boss_h);
    for (dx = [-1, 1])
        translate([usbc_trigger_x + dx*(usbc_trigger_board_w/2 - 3), inner_wall_y + usbc_trigger_board_d - 3, 0])
            standoff_peg_solid(0, 0, usbc_trigger_hole_d, usbc_trigger_boss_h);
}
module main_usbc_trigger_standoffs_holes() {
    inner_wall_y = -(rear_margin - wall);
    for (dx = [-1, 1])
        translate([usbc_trigger_x + dx*(usbc_trigger_board_w/2 - 3), inner_wall_y + 3, 0])
            standoff_peg_hole(0, 0, usbc_trigger_hole_d, usbc_trigger_boss_h);
    for (dx = [-1, 1])
        translate([usbc_trigger_x + dx*(usbc_trigger_board_w/2 - 3), inner_wall_y + usbc_trigger_board_d - 3, 0])
            standoff_peg_hole(0, 0, usbc_trigger_hole_d, usbc_trigger_boss_h);
}
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
