wdathing/coco3-case-project/IMG_9744.jpeg

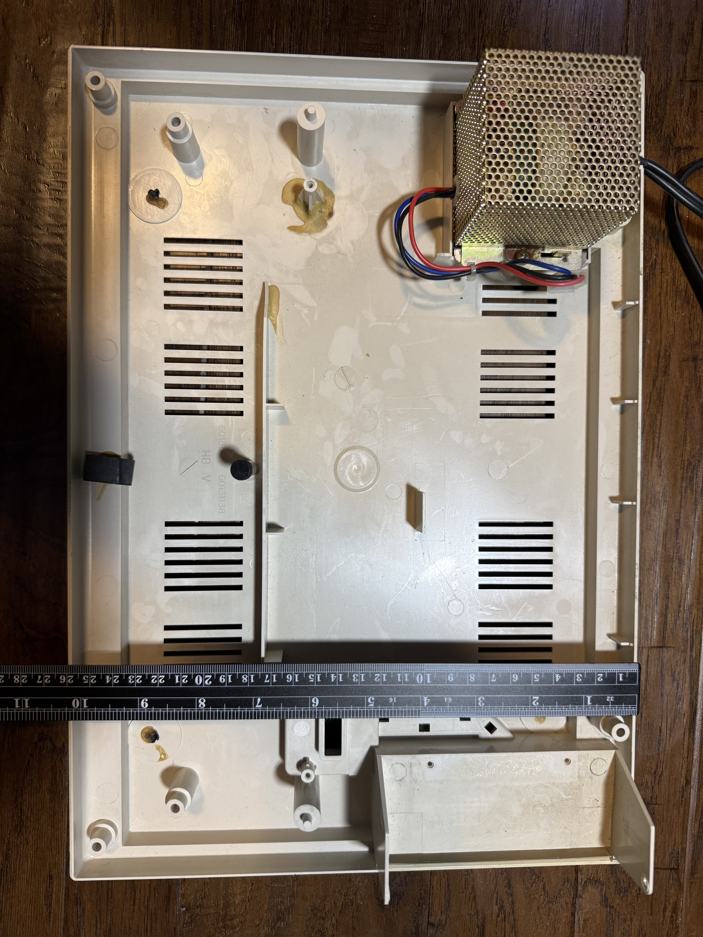
IMG_9744.jpeg
